PubInv/high-amp-controller-board/PublicInvention_KiCad_Library/Parts/USB User Library-10118194.STEP

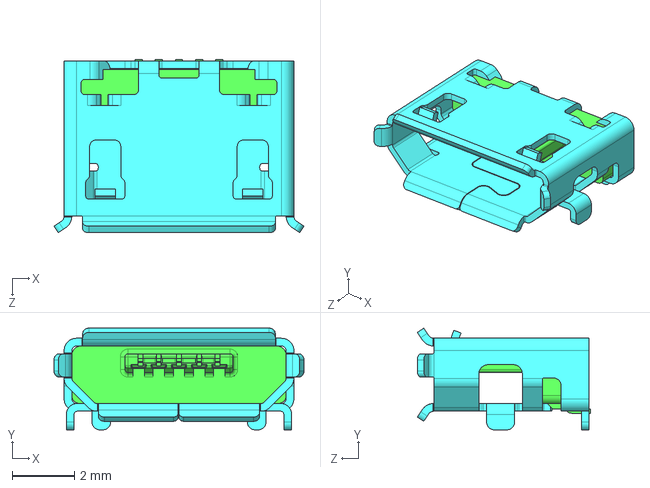
[picture p22: CAD file, 2025-05-26]
PublicInvention_KiCad_Library/Parts/USB User Library-10118194.STEP
8.05 x 3.28 x 5.58 mm
