PubInv/high-amp-controller-board/PublicInvention_KiCad_Library/Parts/12mmx12mm With Green cap.stp

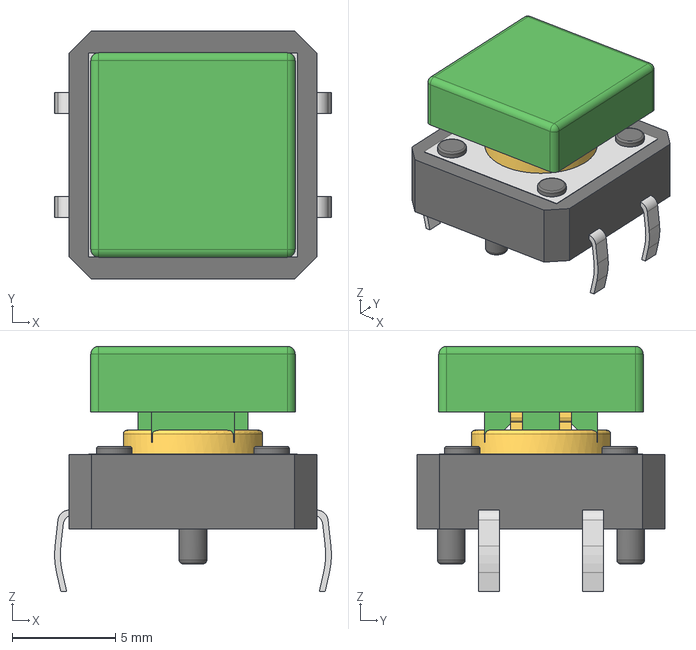
[picture p23: CAD file, 2025-05-26]
PublicInvention_KiCad_Library/Parts/12mmx12mm With Green cap.stp
13.4 x 12.0 x 11.9 mm
Tactal Switch - THRU(12mmx12mmx__mm)-Square Yellow
12mm Cap
