PubInv/high-amp-controller-board/PublicInvention_KiCad_Library/Parts/SOT23.STEP

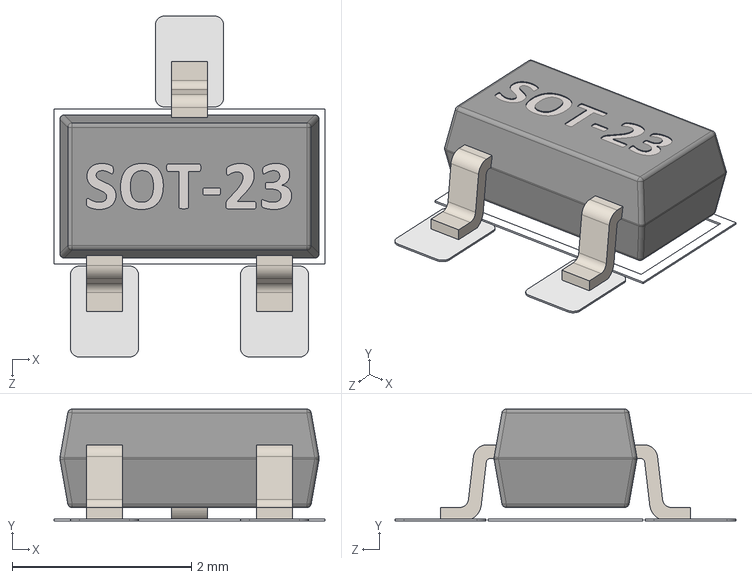
[picture p24: CAD file, 2025-05-26]
PublicInvention_KiCad_Library/Parts/SOT23.STEP
3.03 x 1.25 x 3.81 mm
