PubInv/high-amp-controller-board/PublicInvention_KiCad_Library/Parts/NotGood_XKB Connectivity U254-051N-4BH806.step

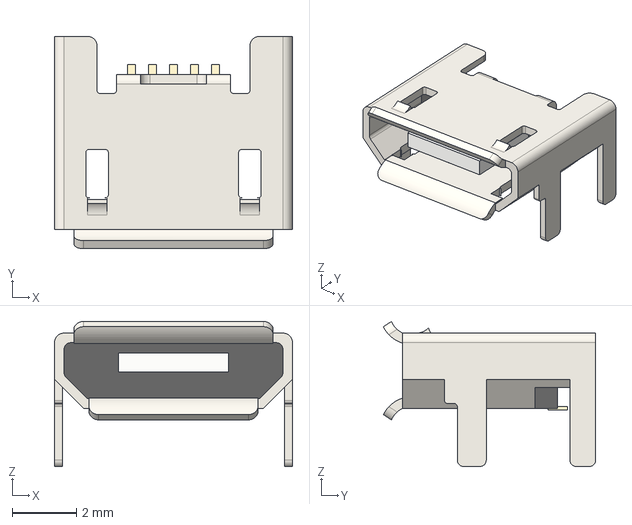
[picture p25: CAD file, 2025-05-26]
PublicInvention_KiCad_Library/Parts/NotGood_XKB Connectivity U254-051N-4BH806.step
7.40 x 6.60 x 4.51 mm
