PubInv/high-amp-controller-board/PublicInvention_KiCad_Library/Parts/BarrelJackSMD v3.step

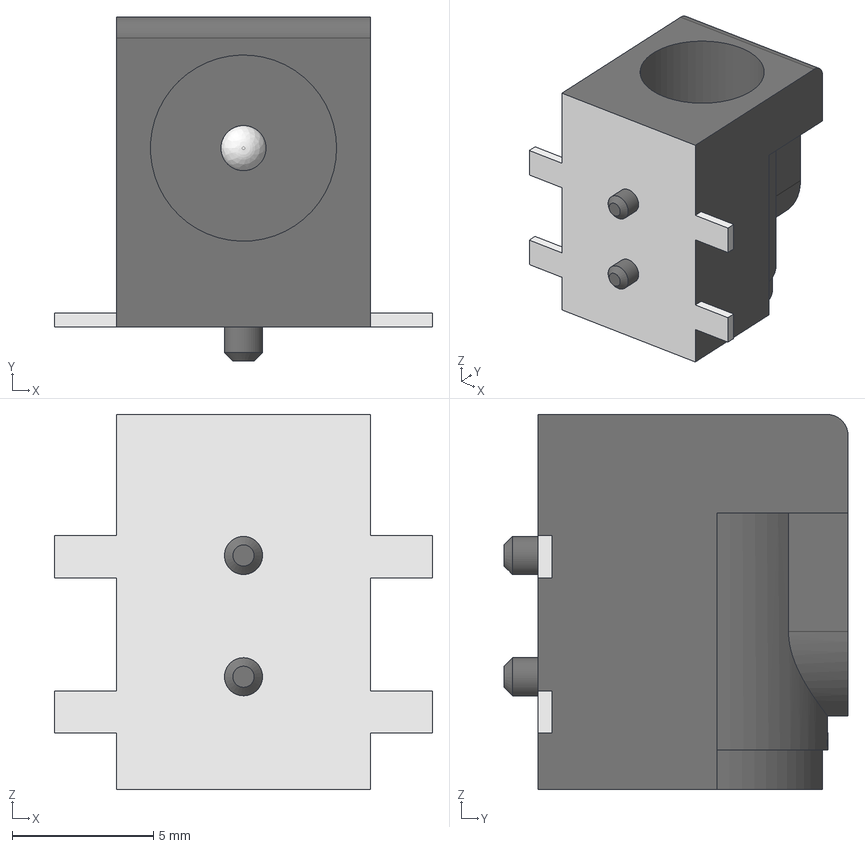
[picture p26: CAD file, 2025-05-26]
PublicInvention_KiCad_Library/Parts/BarrelJackSMD v3.step
13.4 x 12.2 x 13.3 mm
