PubInv/high-amp-controller-board/PublicInvention_KiCad_Library/Parts/TS6-THT-SQ.step

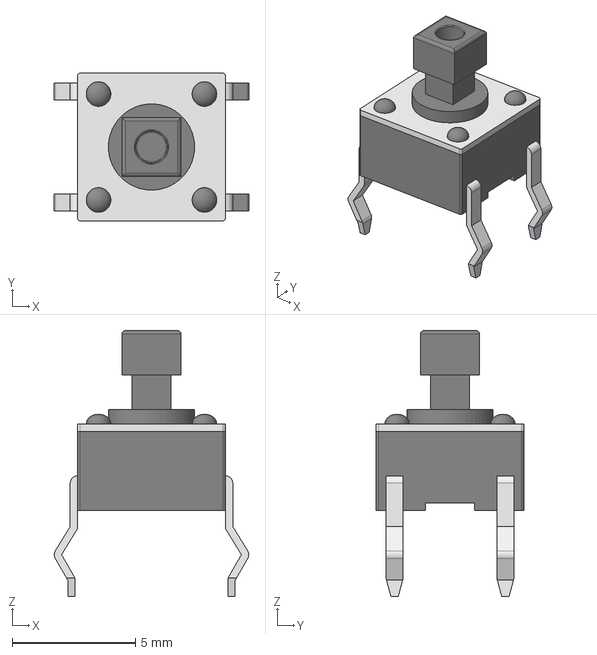
[picture p27: CAD file, 2025-05-26]
PublicInvention_KiCad_Library/Parts/TS6-THT-SQ.step
7.90 x 6.00 x 10.8 mm
