PubInv/high-amp-controller-board/Manufacturing_Files/FabricationPhotos/20250129_134854.jpg

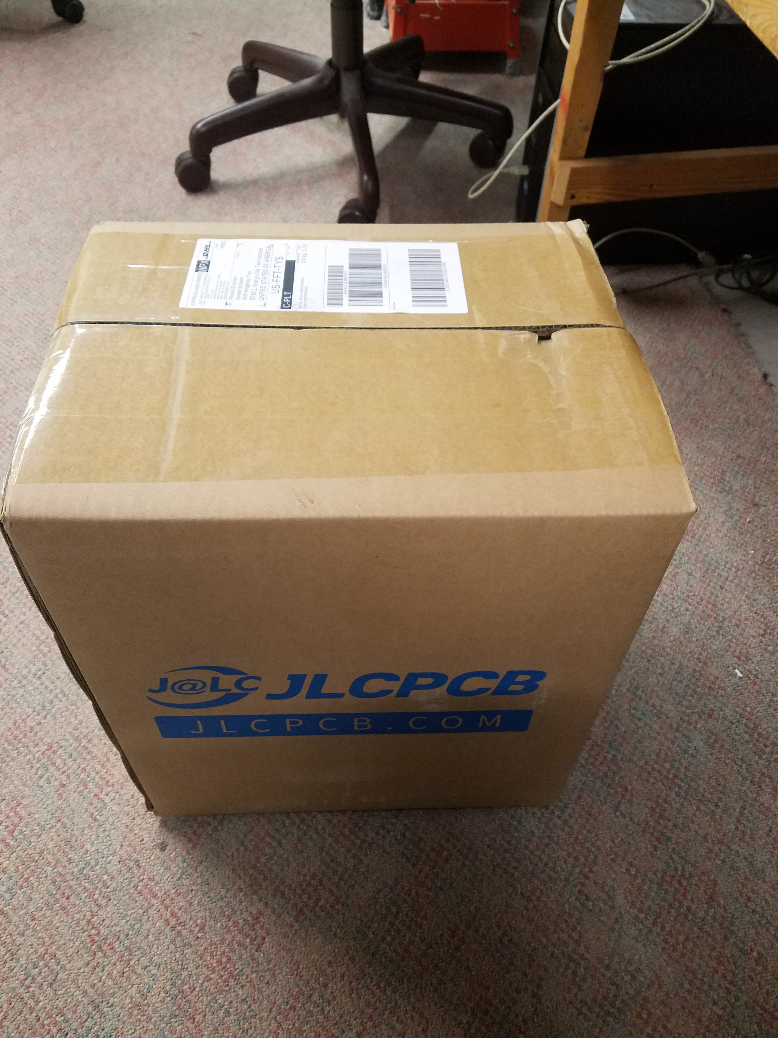
Manufacturing_Files/FabricationPhotos/20250129_134854.jpg
