PubInv/high-amp-controller-board/Adafruit-MAX31850-thermocouple-breakout-board.kicad_sch

## KiCad design Adafruit-MAX31850-thermocouple-breakout-board.kicad_sch (2025-05-26)

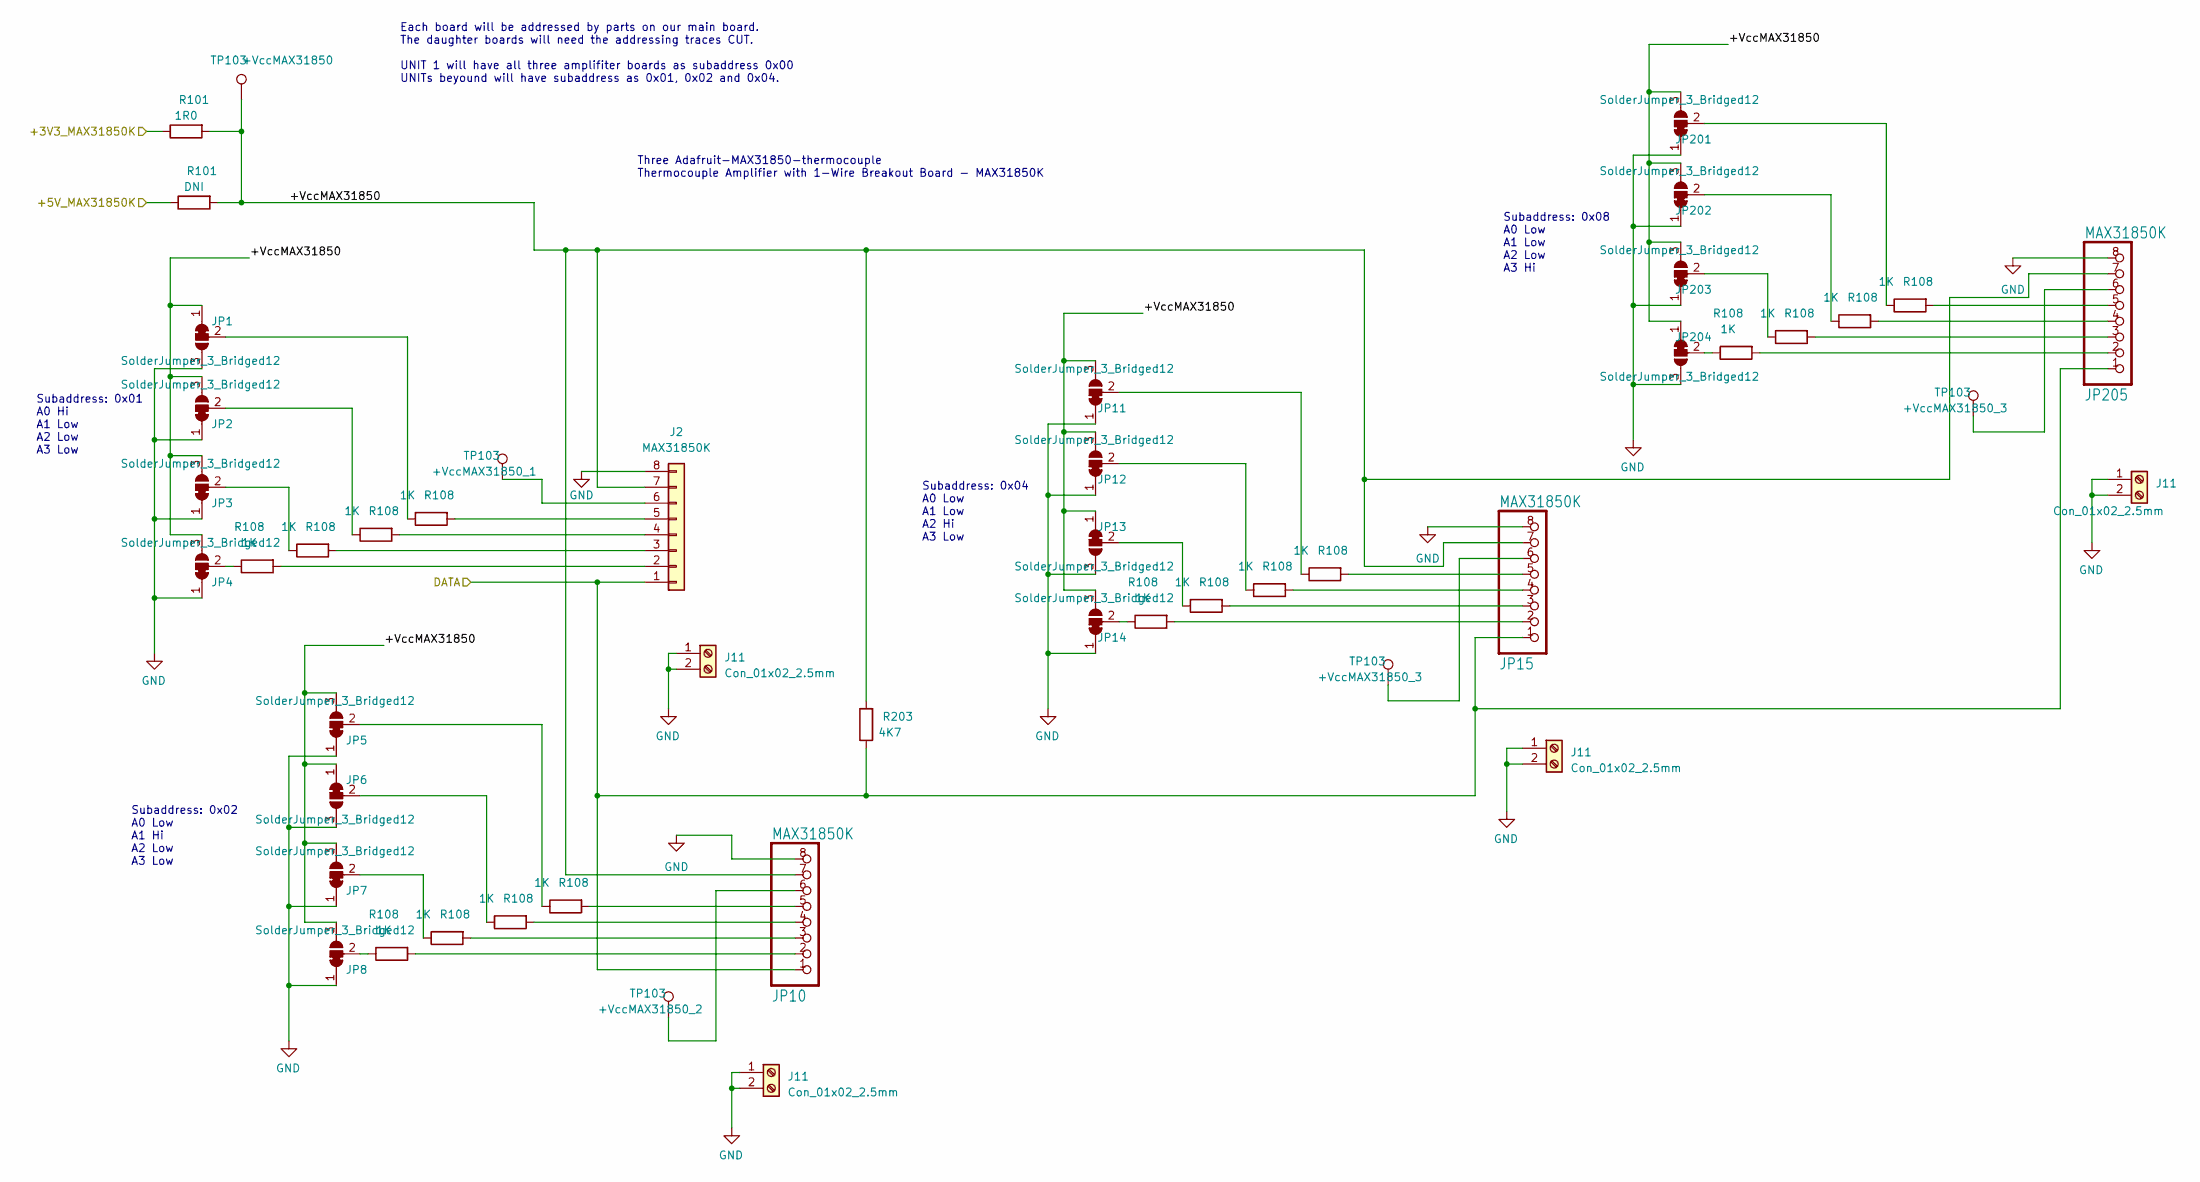
[picture p30: schematic Adafruit-MAX31850-thermocouple-breakout-board.kicad_sch]

Parts:
J2: MAX31850K; Adafruit_MAX31850K_Module; MPN 1727
J11: Con_01x02_2.5mm; JST_XH_B2B-XH-AM_1x02_P2.50mm_Vertical; MPN B2B-XH-A-GU
JP1, JP2, JP3, JP4, JP5, JP6, JP7, JP8, JP11, JP12, JP13, JP14, JP201, JP202, JP203, JP204: SolderJumper_3_Bridged12; SolderJumper-3_P1.3mm_Bridged12_RoundedPad1.0x1.5mm; MPN NA
JP10, JP15, JP205: MAX31850K; Adafruit_MAX31850K_Module; MPN 1727
R101: 1R0; R_0603_1608Metric_Pad0.98x0.95mm_HandSolder; MPN RMC060315%N
R108: 1K; R_0603_1608Metric_Pad0.98x0.95mm_HandSolder; MPN RMC06031K1%N
R203: 4K7; R_0603_1608Metric_Pad0.98x0.95mm_HandSolder; MPN RMC 0603 4K7 F N
TP103: +VccMAX31850; TestPoint_Loop_D2.54mm_Drill1.5mm_Beaded; MPN RH-5000

Connections:
+3V3_MAX31850K: R101.1
+5V_MAX31850K: R101.1
+VccMAX31850: J2.7, JP1.1 (A), JP2.3 (B), JP3.3 (B), JP4.3 (B), JP5.3 (B), JP6.1 (A), JP7.3 (B), JP8.3 (B), JP10.7, JP11.3 (B), JP12.3 (B), JP13.1 (A), JP14.3 (B), JP15.7, JP201.3 (B), JP202.3 (B), JP203.3 (B), JP204.1 (A), JP205.7, R101.2, R203.2, TP103.1
DATA: J2.1, JP10.1, JP15.1, JP205.1, R203.1
GND: J2.8, J11.1, J11.2, JP1.3 (B), JP2.1 (A), JP3.1 (A), JP4.1 (A), JP5.1 (A), JP6.3 (B), JP7.1 (A), JP8.1 (A), JP10.8, JP11.1 (A), JP12.1 (A), JP13.3 (B), JP14.1 (A), JP15.8, JP201.1 (A), JP202.1 (A), JP203.1 (A), JP204.3 (B), JP205.8
unnamed: J2.2, R108.2
unnamed: J2.3, R108.2
unnamed: J2.4, R108.2
unnamed: J2.5, R108.2
unnamed: J2.6, TP103.1
unnamed: JP1.2 (C), R108.1
unnamed: JP2.2 (C), R108.1
unnamed: JP3.2 (C), R108.1
unnamed: JP4.2 (C), R108.1
unnamed: JP5.2 (C), R108.1
unnamed: JP6.2 (C), R108.1
unnamed: JP7.2 (C), R108.1
unnamed: JP8.2 (C), R108.1
unnamed: JP10.2, R108.2
unnamed: JP10.3, R108.2
unnamed: JP10.4, R108.2
unnamed: JP10.5, R108.2
unnamed: JP10.6, TP103.1
unnamed: JP11.2 (C), R108.1
unnamed: JP12.2 (C), R108.1
unnamed: JP13.2 (C), R108.1
unnamed: JP14.2 (C), R108.1
unnamed: JP15.2, R108.2
unnamed: JP15.3, R108.2
unnamed: JP15.4, R108.2
unnamed: JP15.5, R108.2
unnamed: JP15.6, TP103.1
unnamed: JP201.2 (C), R108.1
unnamed: JP202.2 (C), R108.1
unnamed: JP203.2 (C), R108.1
unnamed: JP204.2 (C), R108.1
unnamed: JP205.2, R108.2
unnamed: JP205.3, R108.2
unnamed: JP205.4, R108.2
unnamed: JP205.5, R108.2
unnamed: JP205.6, TP103.1

Notes on the sheet:
Subaddress: 0x02 A0 Low A1 Hi A2 Low A3 Low
Subaddress: 0x04 A0 Low A1 Low A2 Hi A3 Low
Subaddress: 0x01 A0 Hi A1 Low A2 Low A3 Low
Each board will be addressed by parts on our main board. The daughter boards will need the addressing traces CUT. UNIT 1 will have all three amplifiter boards as subaddress 0x00 UNITs beyound will have subaddress as 0x01, 0x02 and 0x04.
Three Adafruit-MAX31850-thermocouple Thermocouple Amplifier with 1-Wire Breakout Board - MAX31850K
Subaddress: 0x08 A0 Low A1 Low A2 Low A3 Hi
