PubInv/high-amp-controller-board/Adafruit-MAX31855-breakout-board.kicad_sch

## KiCad design Adafruit-MAX31855-breakout-board.kicad_sch (2025-05-26)

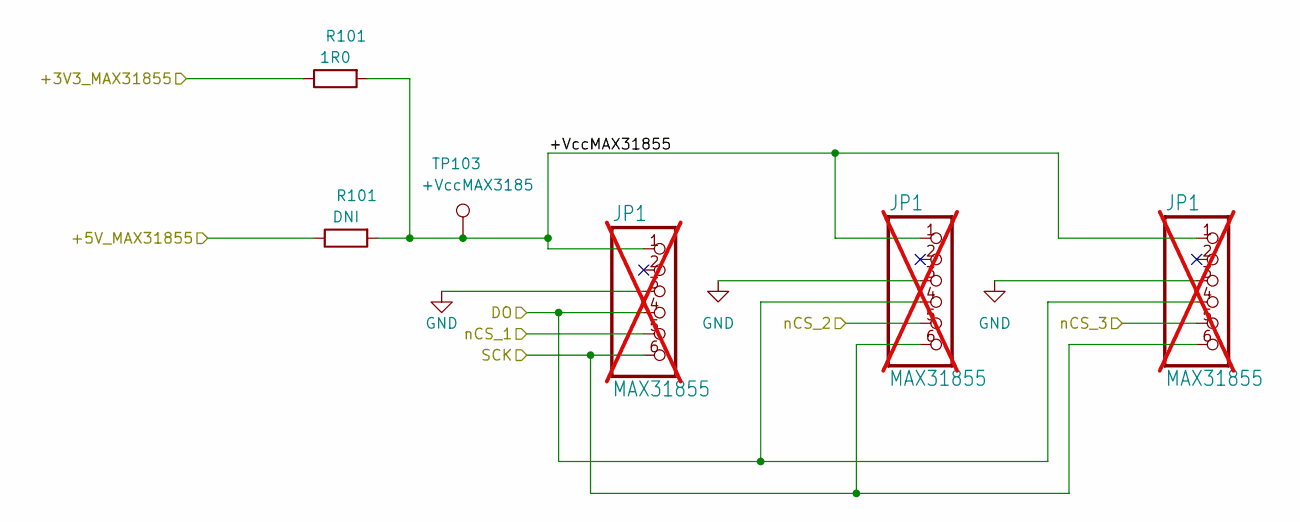
[picture p31: schematic Adafruit-MAX31855-breakout-board.kicad_sch]

Parts:
JP1: MAX31855; Adafruit_MAX31855_Module; MPN 269; not fitted
R101: 1R0; R_0603_1608Metric_Pad0.98x0.95mm_HandSolder; MPN RMC060315%N
TP103: +VccMAX3185; TestPoint_Loop_D2.54mm_Drill1.5mm_Beaded; MPN RH-5000

Connections:
+3V3_MAX31855: R101.1
+5V_MAX31855: R101.1
+VccMAX31855: JP1.1, R101.2, TP103.1
DO: JP1.4
GND: JP1.3
SCK: JP1.6
nCS_1: JP1.5
nCS_2: JP1.5
nCS_3: JP1.5
