PubInv/high-amp-controller-board/Adafruit-MAX31856-PCB-master.kicad_sch

## KiCad design Adafruit-MAX31856-PCB-master.kicad_sch (2025-05-26)

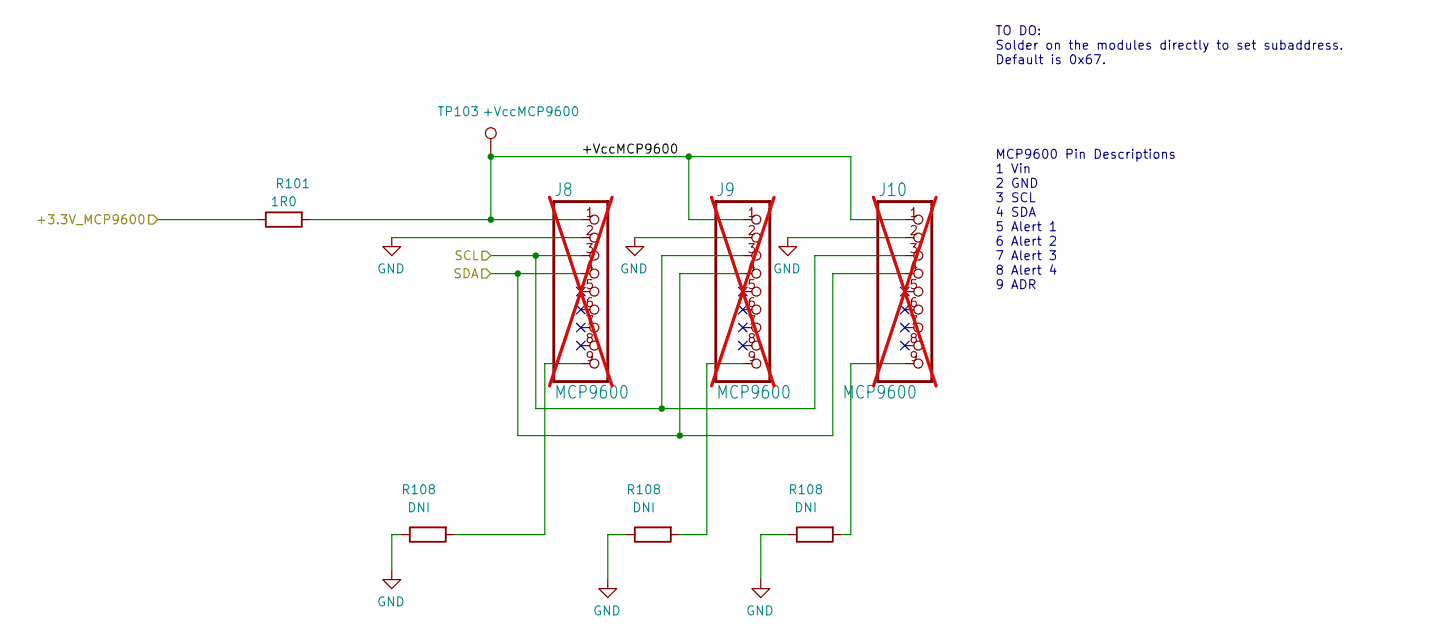
[picture p32: schematic Adafruit-MAX31856-PCB-master.kicad_sch]

Parts:
J8, J9, J10: MCP9600; Adafruit_MCP9600_Module; MPN 4101; not fitted
R101: 1R0; R_0603_1608Metric_Pad0.98x0.95mm_HandSolder; MPN RMC060315%N
R108: DNI; R_0603_1608Metric_Pad0.98x0.95mm_HandSolder; MPN RMC06031K1%N
TP103: +VccMCP9600; TestPoint_Loop_D2.54mm_Drill1.5mm_Beaded; MPN RH-5000

Connections:
+3.3V_MCP9600: R101.1
+VccMCP9600: J8.1, J9.1, J10.1, R101.2, TP103.1
GND: J8.2, J9.2, J10.2, R108.1
unnamed: J8.9, R108.2
unnamed: J9.9, R108.2
unnamed: J10.9, R108.2
SCL: J8.3, J9.3, J10.3
SDA: J8.4, J9.4, J10.4

Notes on the sheet:
MCP9600 Pin Descriptions 1 Vin 2 GND 3 SCL 4 SDA 5 Alert 1 6 Alert 2 7 Alert 3 8 Alert 4 9 ADR
TO DO: Solder on the modules directly to set subaddress. Default is 0x67.
