PubInv/high-amp-controller-board/BreadBoard30P.kicad_sch

## KiCad design BreadBoard30P.kicad_sch (2025-05-26)

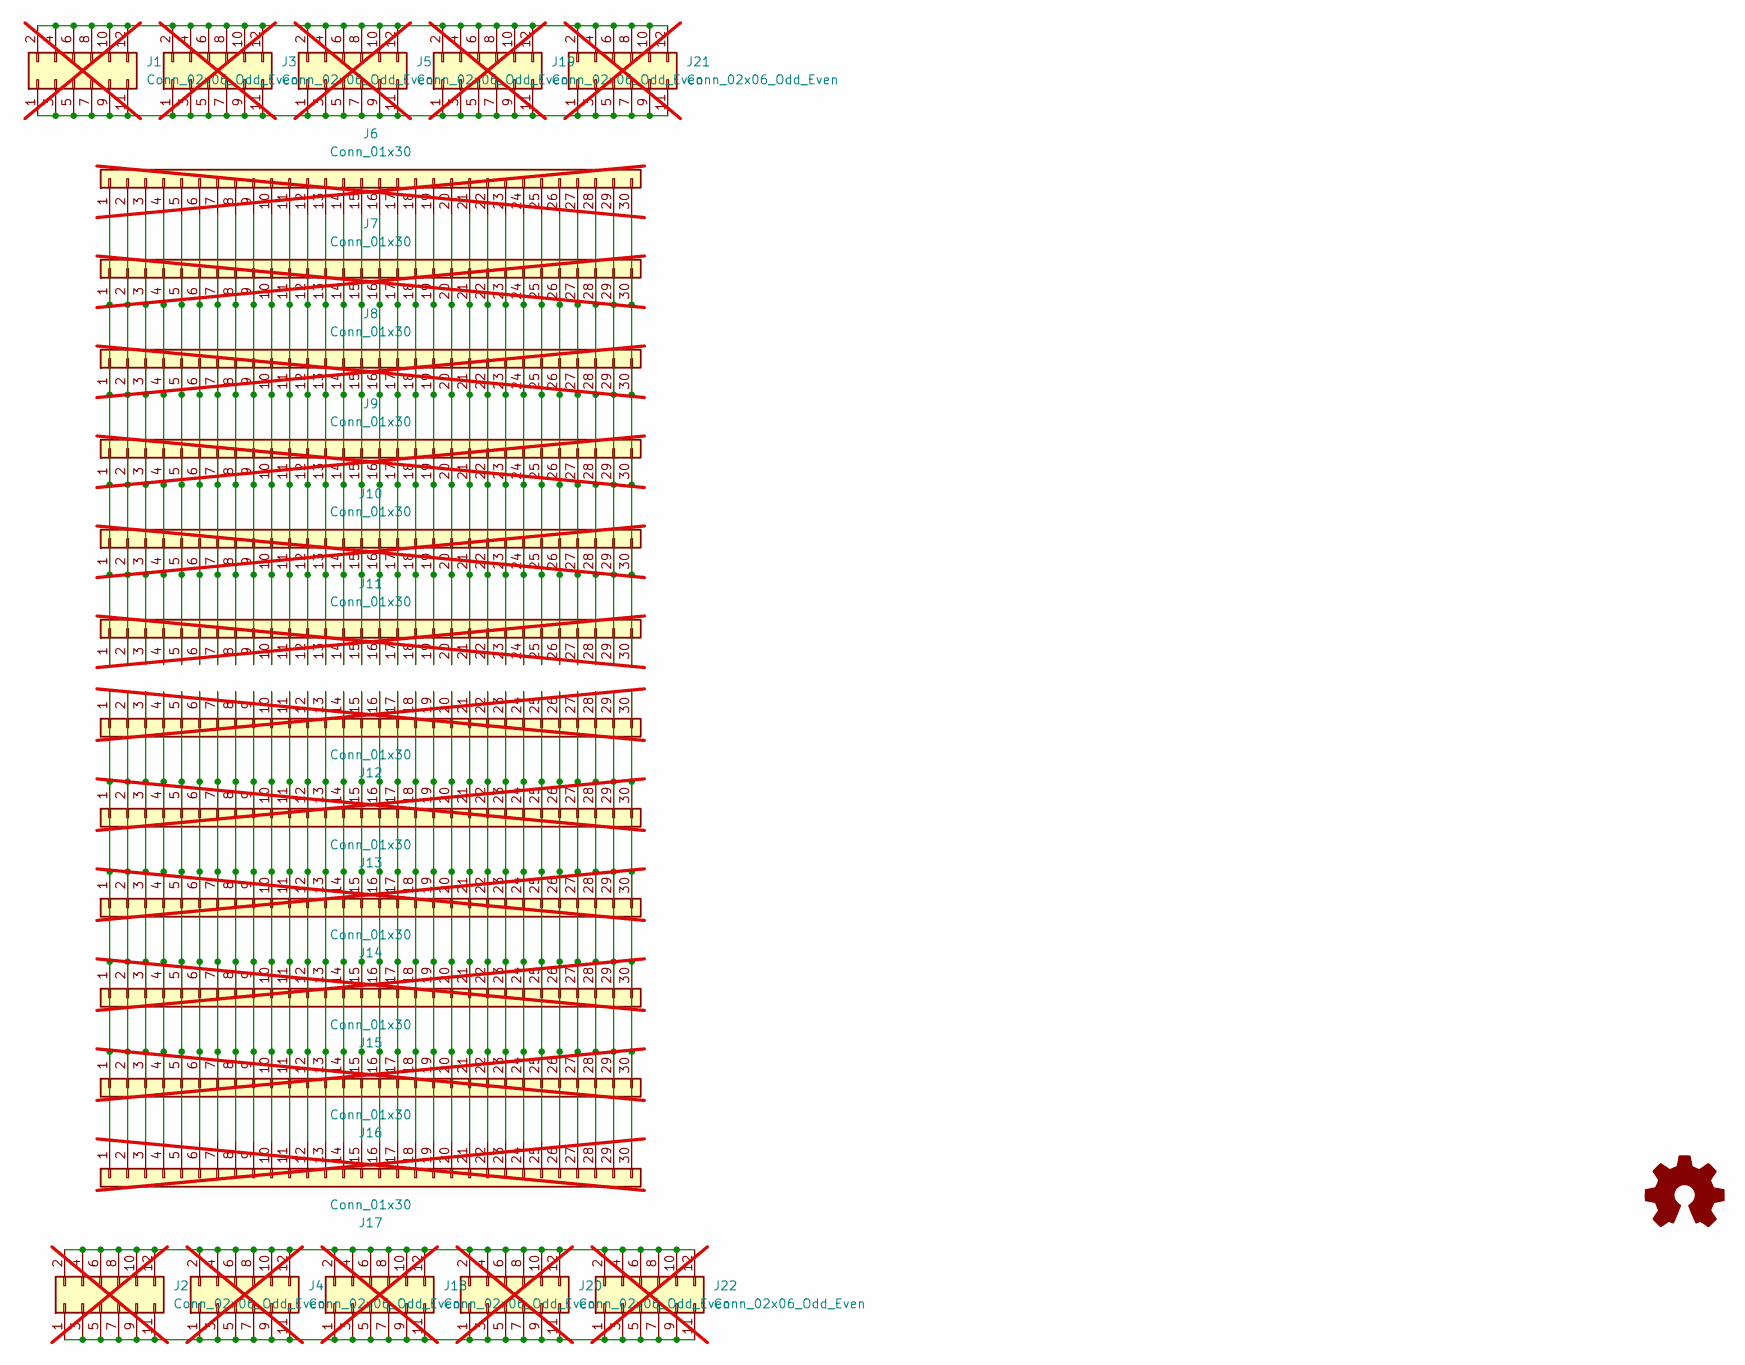
[picture p33: schematic BreadBoard30P.kicad_sch]

Parts:
J1, J2, J3, J4, J5, J18, J19, J20, J21, J22: Conn_02x06_Odd_Even; PinSocket_2x06_P2.54mm_Vertical; not fitted
J6, J7, J8, J9, J10, J11, J12, J13, J14, J15, J16, J17: Conn_01x30; PinSocket_1x30_P2.54mm_Vertical; not fitted

Connections:
unnamed: J1.1, J1.3, J1.5, J1.7, J1.9, J1.11, J3.1, J3.3, J3.5, J3.7, J3.9, J3.11, J5.1, J5.3, J5.5, J5.7, J5.9, J5.11, J19.1, J19.3, J19.5, J19.7, J19.9, J19.11, J21.1, J21.3, J21.5, J21.7, J21.9, J21.11
unnamed: J1.2, J1.4, J1.6, J1.8, J1.10, J1.12, J3.2, J3.4, J3.6, J3.8, J3.10, J3.12, J5.2, J5.4, J5.6, J5.8, J5.10, J5.12, J19.2, J19.4, J19.6, J19.8, J19.10, J19.12, J21.2, J21.4, J21.6, J21.8, J21.10, J21.12
unnamed: J6.1, J7.1, J8.1, J9.1, J10.1, J11.1
unnamed: J6.2, J7.2, J8.2, J9.2, J10.2, J11.2
unnamed: J6.3, J7.3, J8.3, J9.3, J10.3, J11.3
unnamed: J6.4, J7.4, J8.4, J9.4, J10.4, J11.4
unnamed: J6.5, J7.5, J8.5, J9.5, J10.5, J11.5
unnamed: J6.6, J7.6, J8.6, J9.6, J10.6, J11.6
unnamed: J6.7, J7.7, J8.7, J9.7, J10.7, J11.7
unnamed: J6.8, J7.8, J8.8, J9.8, J10.8, J11.8
unnamed: J6.9, J7.9, J8.9, J9.9, J10.9, J11.9
unnamed: J6.10, J7.10, J8.10, J9.10, J10.10, J11.10
unnamed: J6.11, J7.11, J8.11, J9.11, J10.11, J11.11
unnamed: J6.12, J7.12, J8.12, J9.12, J10.12, J11.12
unnamed: J6.13, J7.13, J8.13, J9.13, J10.13, J11.13
unnamed: J6.14, J7.14, J8.14, J9.14, J10.14, J11.14
unnamed: J6.15, J7.15, J8.15, J9.15, J10.15, J11.15
unnamed: J6.16, J7.16, J8.16, J9.16, J10.16, J11.16
unnamed: J6.17, J7.17, J8.17, J9.17, J10.17, J11.17
unnamed: J6.18, J7.18, J8.18, J9.18, J10.18, J11.18
unnamed: J6.19, J7.19, J8.19, J9.19, J10.19, J11.19
unnamed: J6.20, J7.20, J8.20, J9.20, J10.20, J11.20
unnamed: J6.21, J7.21, J8.21, J9.21, J10.21, J11.21
unnamed: J6.22, J7.22, J8.22, J9.22, J10.22, J11.22
unnamed: J6.23, J7.23, J8.23, J9.23, J10.23, J11.23
unnamed: J6.24, J7.24, J8.24, J9.24, J10.24, J11.24
unnamed: J6.25, J7.25, J8.25, J9.25, J10.25, J11.25
unnamed: J6.26, J7.26, J8.26, J9.26, J10.26, J11.26
unnamed: J6.27, J7.27, J8.27, J9.27, J10.27, J11.27
unnamed: J6.28, J7.28, J8.28, J9.28, J10.28, J11.28
unnamed: J6.29, J7.29, J8.29, J9.29, J10.29, J11.29
unnamed: J6.30, J7.30, J8.30, J9.30, J10.30, J11.30
unnamed: J12.1, J13.1, J14.1, J15.1, J16.1, J17.1
unnamed: J12.2, J13.2, J14.2, J15.2, J16.2, J17.2
unnamed: J12.3, J13.3, J14.3, J15.3, J16.3, J17.3
unnamed: J12.4, J13.4, J14.4, J15.4, J16.4, J17.4
unnamed: J12.5, J13.5, J14.5, J15.5, J16.5, J17.5
unnamed: J12.6, J13.6, J14.6, J15.6, J16.6, J17.6
unnamed: J12.7, J13.7, J14.7, J15.7, J16.7, J17.7
unnamed: J12.8, J13.8, J14.8, J15.8, J16.8, J17.8
unnamed: J12.9, J13.9, J14.9, J15.9, J16.9, J17.9
unnamed: J12.10, J13.10, J14.10, J15.10, J16.10, J17.10
unnamed: J12.11, J13.11, J14.11, J15.11, J16.11, J17.11
unnamed: J12.12, J13.12, J14.12, J15.12, J16.12, J17.12
unnamed: J12.13, J13.13, J14.13, J15.13, J16.13, J17.13
unnamed: J12.14, J13.14, J14.14, J15.14, J16.14, J17.14
unnamed: J12.15, J13.15, J14.15, J15.15, J16.15, J17.15
unnamed: J12.16, J13.16, J14.16, J15.16, J16.16, J17.16
unnamed: J12.17, J13.17, J14.17, J15.17, J16.17, J17.17
unnamed: J12.18, J13.18, J14.18, J15.18, J16.18, J17.18
unnamed: J12.19, J13.19, J14.19, J15.19, J16.19, J17.19
unnamed: J12.20, J13.20, J14.20, J15.20, J16.20, J17.20
unnamed: J12.21, J13.21, J14.21, J15.21, J16.21, J17.21
unnamed: J12.22, J13.22, J14.22, J15.22, J16.22, J17.22
unnamed: J12.23, J13.23, J14.23, J15.23, J16.23, J17.23
unnamed: J12.24, J13.24, J14.24, J15.24, J16.24, J17.24
unnamed: J12.25, J13.25, J14.25, J15.25, J16.25, J17.25
unnamed: J12.26, J13.26, J14.26, J15.26, J16.26, J17.26
unnamed: J12.27, J13.27, J14.27, J15.27, J16.27, J17.27
unnamed: J12.28, J13.28, J14.28, J15.28, J16.28, J17.28
unnamed: J12.29, J13.29, J14.29, J15.29, J16.29, J17.29
unnamed: J12.30, J13.30, J14.30, J15.30, J16.30, J17.30
unnamed: J2.1, J2.3, J2.5, J2.7, J2.9, J2.11, J4.1, J4.3, J4.5, J4.7, J4.9, J4.11, J18.1, J18.3, J18.5, J18.7, J18.9, J18.11, J20.1, J20.3, J20.5, J20.7, J20.9, J20.11, J22.1, J22.3, J22.5, J22.7, J22.9, J22.11
unnamed: J2.2, J2.4, J2.6, J2.8, J2.10, J2.12, J4.2, J4.4, J4.6, J4.8, J4.10, J4.12, J18.2, J18.4, J18.6, J18.8, J18.10, J18.12, J20.2, J20.4, J20.6, J20.8, J20.10, J20.12, J22.2, J22.4, J22.6, J22.8, J22.10, J22.12
