PubInv/high-amp-controller-board/Control_1v2.kicad_sch

## KiCad design Control_1v2.kicad_sch (2025-05-26)

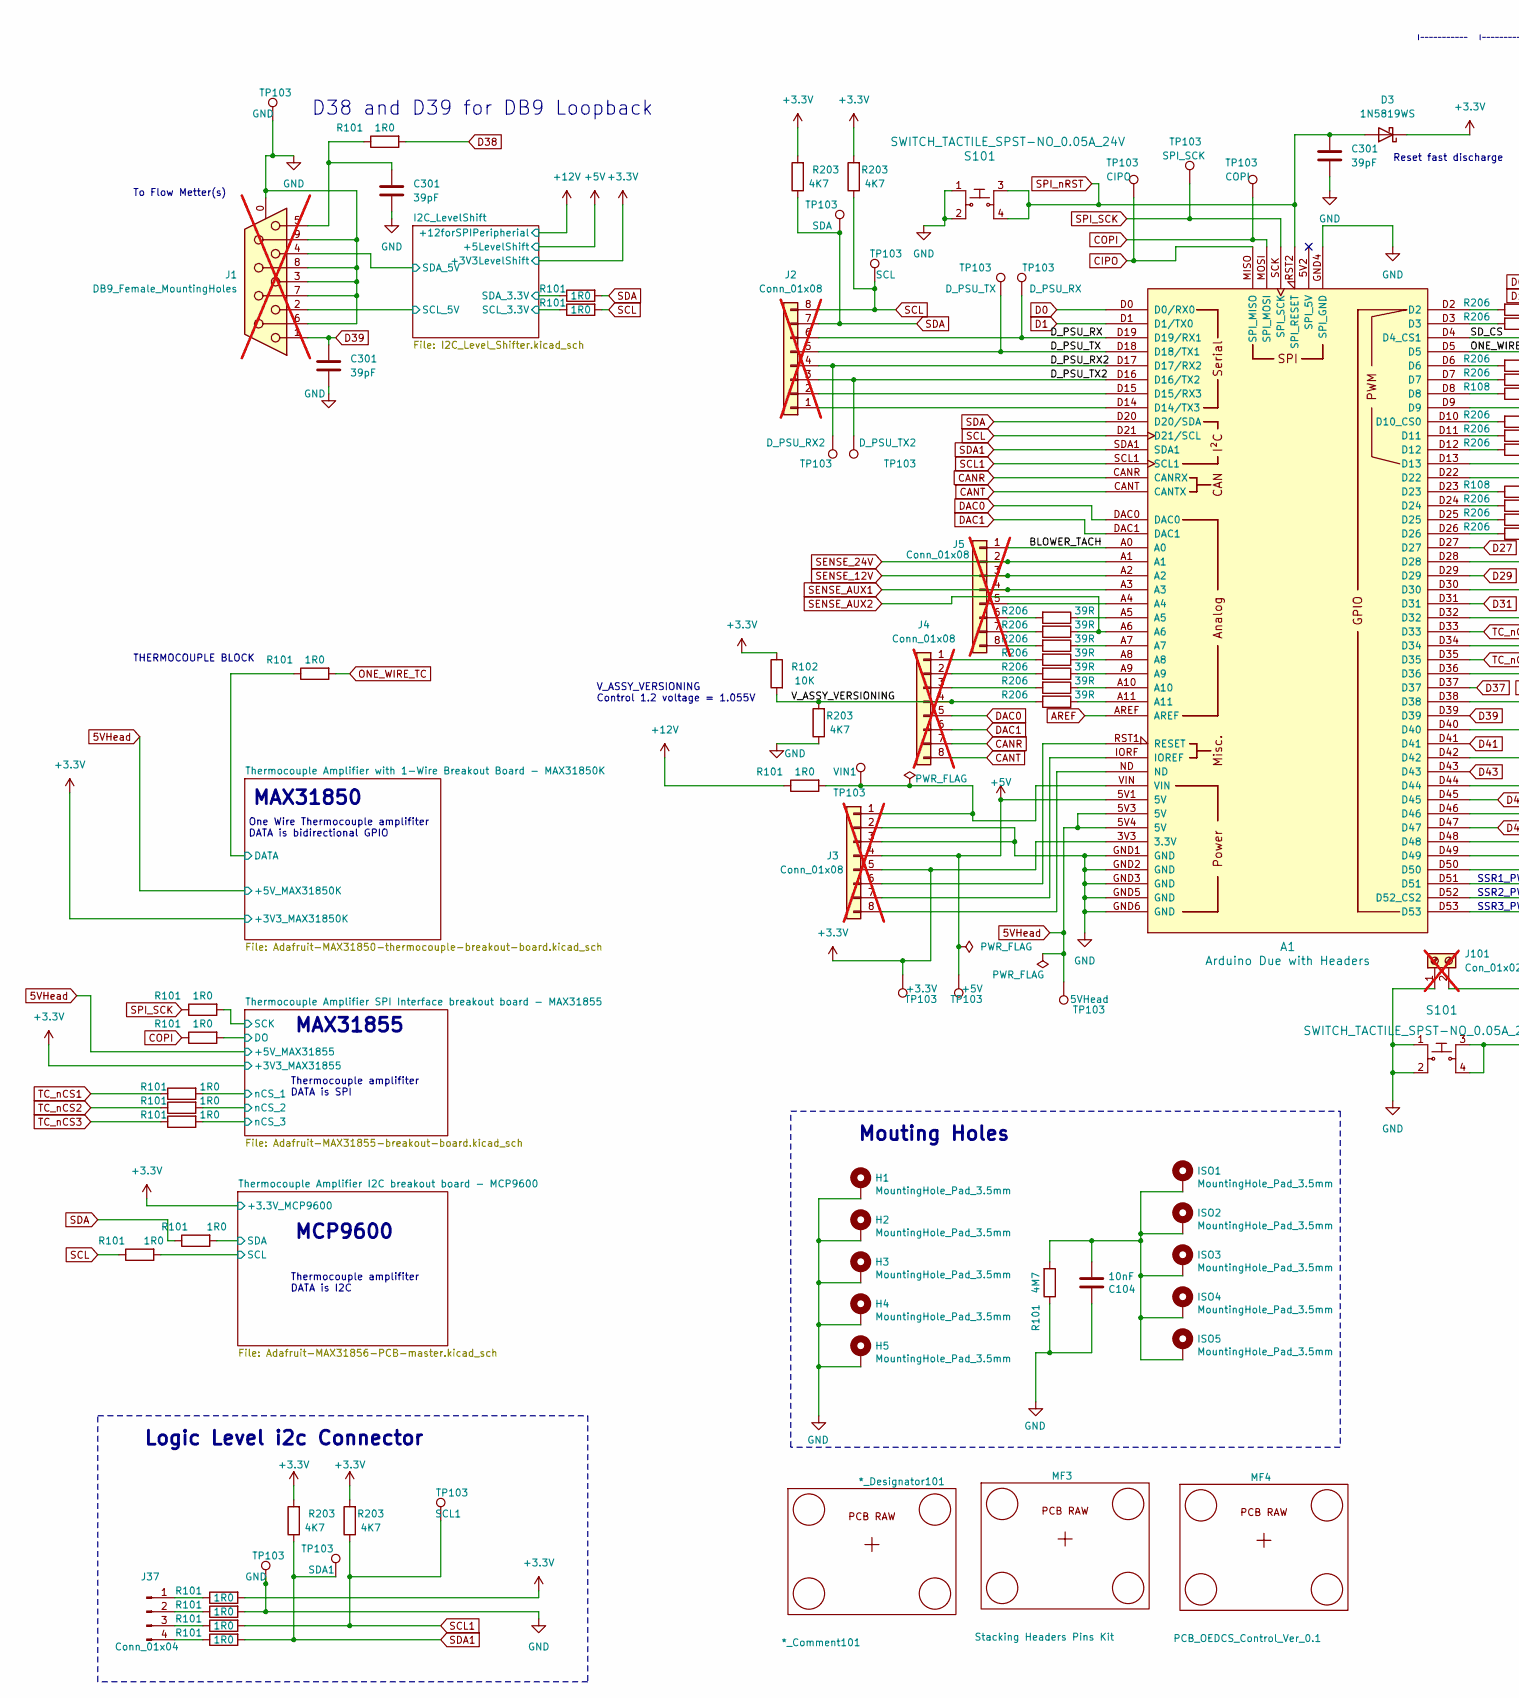
[picture p34: schematic Control_1v2.kicad_sch, part in row 1, column 1]

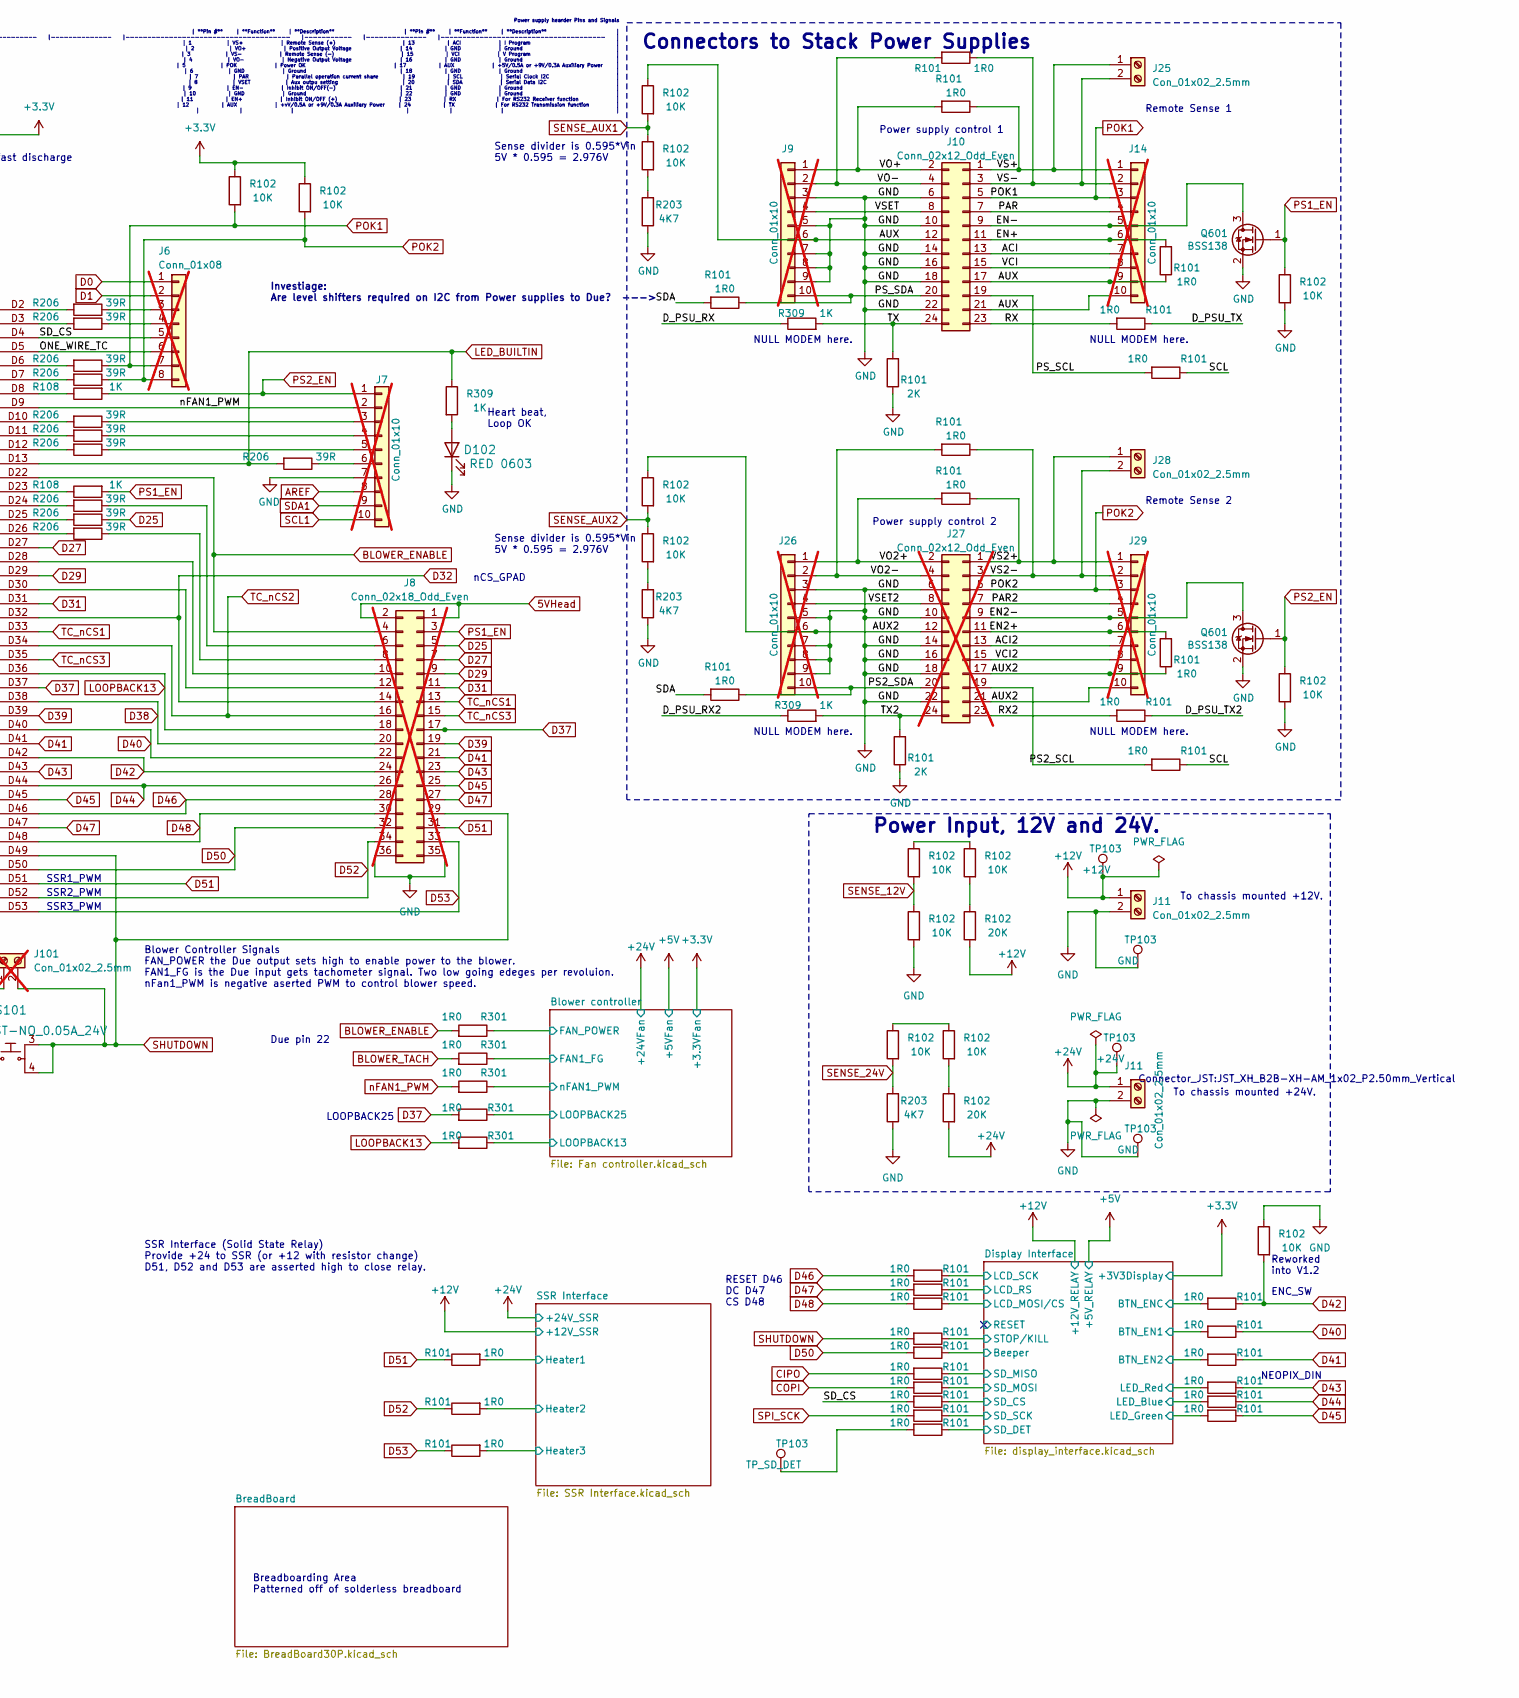
[picture p35: schematic Control_1v2.kicad_sch, part in row 1, column 2]

Parts:
*_Designator101: *_Comment101; Footprint; MPN na
A1: Arduino Due with Headers; Arduino_Due_Shield_Annotated; MPN DUE
C104: 10nF; C_0603_1608Metric_Pad1.08x0.95mm_HandSolder; MPN CC0603JRNPO9BN103
C301: 39pF; C_0603_1608Metric_Pad1.08x0.95mm_HandSolder; MPN CC0603JRNPO9BN390
D3: 1N5819WS; D_SOD-323; MPN 1N5819WS
D102: RED 0603; LED_0603_1608Metric_Pad1.05x0.95mm_HandSolder; MPN LTST-C171KRKT; Digi-Key_PN 160-1427-1-ND
H1, H2, H3, H4, H5: MountingHole_Pad_3.5mm; MountingHole_3.5mm_Pad_Via
ISO1, ISO2, ISO3, ISO4, ISO5: MountingHole_Pad_3.5mm; MountingHole_3.5mm_Pad_Via
J1: DB9_Female_MountingHoles; DSUB-9_Female_Horizontal_P2.77x2.84mm_EdgePinOffset4.94mm_H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; MPN D-DMR009PF-D002; not fitted
J2, J3, J4, J5, J6: Conn_01x08; PinSocket_1x08_P2.54mm_Vertical; MPN PZ254-1-08-Z-8.5; not fitted
J7, J9, J14, J26, J29: Conn_01x10; PinSocket_1x10_P2.54mm_Vertical; MPN PZ254-1-10-Z-8.5; not fitted
J8: Conn_02x18_Odd_Even; PinSocket_2x18_P2.54mm_Vertical; not fitted
J10: Conn_02x12_Odd_Even; JST_PHD_B24B-PHDSS_2x12_P2.00mm_Vertical; Part Number B24B-PHDSS
J11, J25, J28: Con_01x02_2.5mm; JST_XH_B2B-XH-AM_1x02_P2.50mm_Vertical; MPN B2B-XH-A-GU
J27: Conn_02x12_Odd_Even; JST_PHD_B24B-PHDSS_2x12_P2.00mm_Vertical; Part Number B24B-PHDSS; not fitted
J37: Conn_01x04; PinHeader_1x04_P2.54mm_Vertical; MPN HB-PH3-25414PB2GOP
J101: Con_01x02_2.5mm; JST_XH_B2B-XH-AM_1x02_P2.50mm_Vertical; MPN B2B-XH-A-GU; not fitted
MF3: Stacking Headers Pins Kit; NA; MPN PCB_BKT_OEDCS_01
MF4: PCB_OEDCS_Control_Ver_0.1; NA; MPN PCB_OEDCS_Control_Ver_0.1
Q601: BSS138; SOT-23; MPN BSS138
R101, R301: 1R0; R_0603_1608Metric_Pad0.98x0.95mm_HandSolder; MPN RMC060315%N
R102: 10K; R_0603_1608Metric_Pad0.98x0.95mm_HandSolder; MPN RMC060310KFN
R108, R309: 1K; R_0603_1608Metric_Pad0.98x0.95mm_HandSolder; MPN RMC06031K1%N
R203: 4K7; R_0603_1608Metric_Pad0.98x0.95mm_HandSolder; MPN RMC 0603 4K7 F N
R206: 39R; R_0603_1608Metric_Pad0.98x0.95mm_HandSolder; MPN RMC0603391%N
S101: SWITCH_TACTILE_SPST-NO_0.05A_24V; Switch_Tactile_THT_6x6mm; MPN TE Connectivity 1825910-7, Dongguan Gua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
TP103: SPI_SCK; TestPoint_Loop_D2.54mm_Drill1.5mm_Beaded; MPN RH-5004

Connections:
5VHead: A1.5V3 (5V), A1.5V4 (5V), J8.1, J8.2, TP103.1
+3.3V: A1.3V3 (3.3V), D3.1 (K), J3.5, R101.2, R102.1, R203.2, TP103.1
+5V: A1.5V1 (5V), J3.4, TP103.1
+12V: J11.1, R101.1, R102.2, TP103.1
+24V: J11.1, R102.2, TP103.1
ACI: J10.13, J14.7
ACI2: J27.13, J29.7
AREF: A1.AREF, J7.8
AUX: J9.6, J10.12, J10.17, J10.21, J14.9, J14.10, R101.1, R102.1
AUX2: J26.6, J27.12, J27.17, J27.21, J29.9, J29.10, R101.1, R102.1
BLOWER_ENABLE: A1.D22, J8.4, R301.2
BLOWER_TACH: A1.A0, J5.1, R301.2
BTN_EN1: R101.2
BTN_EN2: R101.2
BTN_ENC: R101.2
Beeper: R101.1
CANR: A1.CANR (CANRX), J4.7
CANT: A1.CANT (CANTX), J4.8
CIPO: A1.MISO (SPI_MISO), R101.2, TP103.1
COPI: A1.MOSI (SPI_MOSI), R101.1, R101.2, TP103.1
D0: A1.D0 (D0/RX0), J6.1
D1: A1.D1 (D1/TX0), J6.2
D25: J8.5, R206.1
D27: A1.D27, J8.7
D29: A1.D29, J8.9
D31: A1.D31, J8.11
D32: A1.D32, J8.14
D37: A1.D37, J8.17, R301.2
D38: A1.D38, J8.20, R101.2
D39: A1.D39, C301.1, J1.1, J8.19
D40: A1.D40, J8.22, R101.1
D41: A1.D41, J8.21, R101.1
D42: A1.D42, J8.24, R101.1, R102.2
D43: A1.D43, J8.23, R101.1
D44: A1.D44, J8.26, R101.1
D45: A1.D45, J8.25, R101.1
D46: A1.D46, J8.28, R101.2
D47: A1.D47, J8.27, R101.2
D48: A1.D48, J8.30, R101.2
D50: A1.D50, J8.32, R101.2
D51: A1.D51, J8.31, R101.1
D52: A1.D52 (D52_CS2), J8.34, R101.1
D53: A1.D53, J8.33, R101.1
DAC0: A1.DAC0, J4.5
DAC1: A1.DAC1, J4.6
DATA: R101.1
DO: R101.2
D_PSU_RX: A1.D19 (D19/RX1), J2.6, R309.1, TP103.1
D_PSU_RX2: A1.D17 (D17/RX2), J2.4, R309.1, TP103.1
D_PSU_TX: A1.D18 (D18/TX1), J2.5, R101.1, TP103.1
D_PSU_TX2: A1.D16 (D16/TX2), J2.3, R101.1, TP103.1
EN2+: J27.11, J29.6, R101.2
EN2-: J27.9, J29.5, Q601.3 (D)
EN+: J10.11, J14.6, R101.2
EN-: J10.9, J14.5, Q601.3 (D)
FAN1_FG: R301.1
FAN_POWER: R301.1
GND: A1.GND1 (GND), A1.GND2 (GND), A1.GND3 (GND), A1.GND4 (SPI_GND), A1.GND5 (GND), A1.GND6 (GND), C104.1, C301.2, D102.1 (K), H1.1, H2.1, H3.1, H4.1, H5.1, J1.0 (PAD), J1.3, J1.6, J1.7, J1.8, J1.9, J3.2, J3.3, J7.7, J8.35, J8.36, J9.3, J9.5, J9.7, J9.8, J9.9, J10.6, J10.10, J10.14, J10.16, J10.18, J10.22, J11.2, J26.3, J26.5, J26.7, J26.8, J26.9, J27.6, J27.10, J27.14, J27.16, J27.18, J27.22, J101.1, Q601.2 (S), R101.1, R101.2, R102.1, R102.2, R203.1, S101.1, S101.2, TP103.1
Heater1: R101.2
Heater2: R101.2
Heater3: R101.2
LCD_MOSI/CS: R101.1
LCD_RS: R101.1
LCD_SCK: R101.1
LED_BUILTIN: A1.D13, R206.2, R309.1
LED_Blue: R101.2
LED_Green: R101.2
LED_Red: R101.2
LOOPBACK13: A1.D36, J8.18, R301.1, R301.2
LOOPBACK25: R301.1
unnamed: A1.A4, J5.5
unnamed: A1.A5, R206.1
unnamed: A1.A7, R206.1
unnamed: A1.A8, R206.1
unnamed: A1.A9, R206.1
unnamed: A1.A10, R206.1
unnamed: A1.A11, R206.1
unnamed: A1.D2, R206.2
unnamed: A1.D3, R206.2
unnamed: A1.D6, R206.2
unnamed: A1.D7, R206.2
unnamed: A1.D8, R108.1
unnamed: A1.D10 (D10_CS0), R206.2
unnamed: A1.D11, R206.2
unnamed: A1.D12, R206.2
unnamed: A1.D14 (D14/TX3), J2.1
unnamed: A1.D15 (D15/RX3), J2.2
unnamed: A1.D23, R108.1
unnamed: A1.D24, R206.2
unnamed: A1.D25, R206.2
unnamed: A1.D26, R206.2
unnamed: A1.D28, J8.10
unnamed: A1.D30, J8.12
unnamed: A1.IORF (IOREF), J3.7
unnamed: A1.ND, J3.8
unnamed: A1.RST1 (RESET), J3.6
unnamed: A1.VIN, J3.1, R101.2, TP103.1
unnamed: C104.2, ISO1.1, ISO2.1, ISO3.1, ISO4.1, ISO5.1, R101.2
unnamed: C301.1, J1.5, R101.1
unnamed: D102.2 (A), R309.2
unnamed: J4.1, R206.2
unnamed: J4.2, R206.2
unnamed: J4.3, R206.2
unnamed: J5.6, R206.2
unnamed: J5.7, R206.2
unnamed: J5.8, R206.2
unnamed: J6.3, R206.1
unnamed: J6.4, R206.1
unnamed: J7.3, R206.1
unnamed: J7.4, R206.1
unnamed: J7.5, R206.1
unnamed: J7.6, R206.1
unnamed: J8.6, R206.1
unnamed: J8.8, R206.1
unnamed: J37.1, R101.1
unnamed: J37.2, R101.1
unnamed: J37.3, R101.1
unnamed: J37.4, R101.1
unnamed: R101.2, TP103.1
unnamed: R102.1, R102.2
unnamed: R102.2, R203.2
ONE_WIRE_TC: A1.D5, J6.6, R101.2
PAR: J10.7, J14.4
PAR2: J27.7, J29.4
POK1: J6.7, J10.5, J14.3, R102.2, R206.1
POK2: J6.8, J27.5, J29.3, R102.2, R206.1
PS1_EN: J8.3, Q601.1 (G), R102.1, R108.2
PS2_EN: J7.1, Q601.1 (G), R102.1, R108.2
PS2_SCL: J27.19, R101.2
PS2_SDA: J26.10, J27.20, R101.1
PS_SCL: J10.19, R101.2
PS_SDA: J9.10, J10.20, R101.1
RX: J10.23, R101.2
RX2: J27.23, R101.2
SCK: R101.2
SCL: A1.D21 (D21/SCL), J2.8, R101.1, R101.2, R203.1, TP103.1
SCL1: A1.SCL1, J7.10, R101.2, R203.1, TP103.1
SCL_3.3V: R101.1
SCL_5V: J1.2
SDA: A1.D20 (D20/SDA), J2.7, R101.1, R101.2, R203.1, TP103.1
SDA1: A1.SDA1, J7.9, R101.2, R203.1, TP103.1
SDA_3.3V: R101.1
SDA_5V: J1.4
SD_CS: A1.D4 (D4_CS1), J6.5, R101.1, R101.2
SD_DET: R101.1
SD_MISO: R101.1
SD_MOSI: R101.1
SD_SCK: R101.1
SENSE_12V: A1.A2, J5.3, R102.1, R102.2
SENSE_24V: A1.A1, J5.2, R102.2, R203.2
SENSE_AUX1: A1.A3, J5.4, R102.1, R102.2
SENSE_AUX2: A1.A6, R102.1, R102.2, R206.1
SHUTDOWN: A1.D49, J8.29, J101.2, R101.2, S101.3, S101.4
SPI_SCK: A1.SCK (SPI_SCK), R101.1, R101.2, TP103.1
SPI_nRST: A1.RST2 (SPI_RESET), C301.1, D3.2 (A), S101.3, S101.4
STOP/KILL: R101.1
TC_nCS1: A1.D33, J8.13, R101.1
TC_nCS2: A1.D34, J8.16, R101.1
TC_nCS3: A1.D35, J8.15, R101.1
TX: J10.24, R101.2, R309.2
TX2: J27.24, R101.2, R309.2
VCI: J10.15, J14.8
VCI2: J27.15, J29.8
VO2+: J26.1, J27.2, R101.2
VO2-: J26.2, J27.4, R101.2
VO+: J9.1, J10.2, R101.2
VO-: J9.2, J10.4, R101.2
VS2+: J27.1, J28.1, J29.1, R101.1
VS2-: J27.3, J28.2, J29.2, R101.1
VS+: J10.1, J14.1, J25.1, R101.1
VS-: J10.3, J14.2, J25.2, R101.1
VSET: J9.4, J10.8
VSET2: J26.4, J27.8
V_ASSY_VERSIONING: J4.4, R102.2, R203.2, R206.2
nCS_1: R101.2
nCS_2: R101.2
nCS_3: R101.2
nFAN1_PWM: A1.D9, J7.2, R301.1, R301.2

Notes on the sheet:
Reset fast discharge
MCP9600
To Flow Metter(s)
SSR Interface (Solid State Relay) Provide +24 to SSR (or +12 with resistor change) D51, D52 and D53 are asserted high to close relay.
SSR2_PWM
LOOPBACK25
To chassis mounted +12V.
SSR3_PWM
NULL MODEM here.
Remote Sense 1
Power Input, 12V and 24V.
ENC_SW
Blower Controller Signals FAN_POWER the Due output sets high to enable power to the blower. FAN1_FG is the Due input gets tachometer signal. Two low going edeges per revoluion. nFan1_PWM is negative aserted PWM to control blower speed.
NEOPIX_DIN
Investiage: Are level shifters required on I2C from Power supplies to Due? --->
Logic Level i2c Connector
Power supply control 2
Thermocouple amplifiter DATA is I2C
THERMOCOUPLE BLOCK
Mouting Holes
Power supply control 1
Connectors to Stack Power Supplies
Thermocouple amplifiter DATA is SPI
nCS_GPAD
Power supply hearder Pins and Signals | **Pin #** | **Function** | **Description** | **Pin #** | **Function** | **Description** | |----------- |-------------- |-------------------------------------- |----------- |-------------- |-------------------------------------- | | 1 | VS+ | Remote Sense (+) 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
D38 and D39 for DB9 Loopback
Sense divider is 0.595*Vin 5V * 0.595 = 2.976V
Connector_JST:JST_XH_B2B-XH-AM_1x02_P2.50mm_Vertical
SSR1_PWM
Reworked into V1.2
V_ASSY_VERSIONING Control 1.2 voltage = 1.055V
Heart beat, Loop OK
Breadboarding Area Patterned off of solderless breadboard
To chassis mounted +24V.
RESET D46 DC D47 CS D48
One Wire Thermocouple amplifiter DATA is bidirectional GPIO
MAX31855
Remote Sense 2
Due pin 22
MAX31850
