PubInv/high-amp-controller-board/Fan controller.kicad_sch

## KiCad design Fan controller.kicad_sch (2025-05-26)

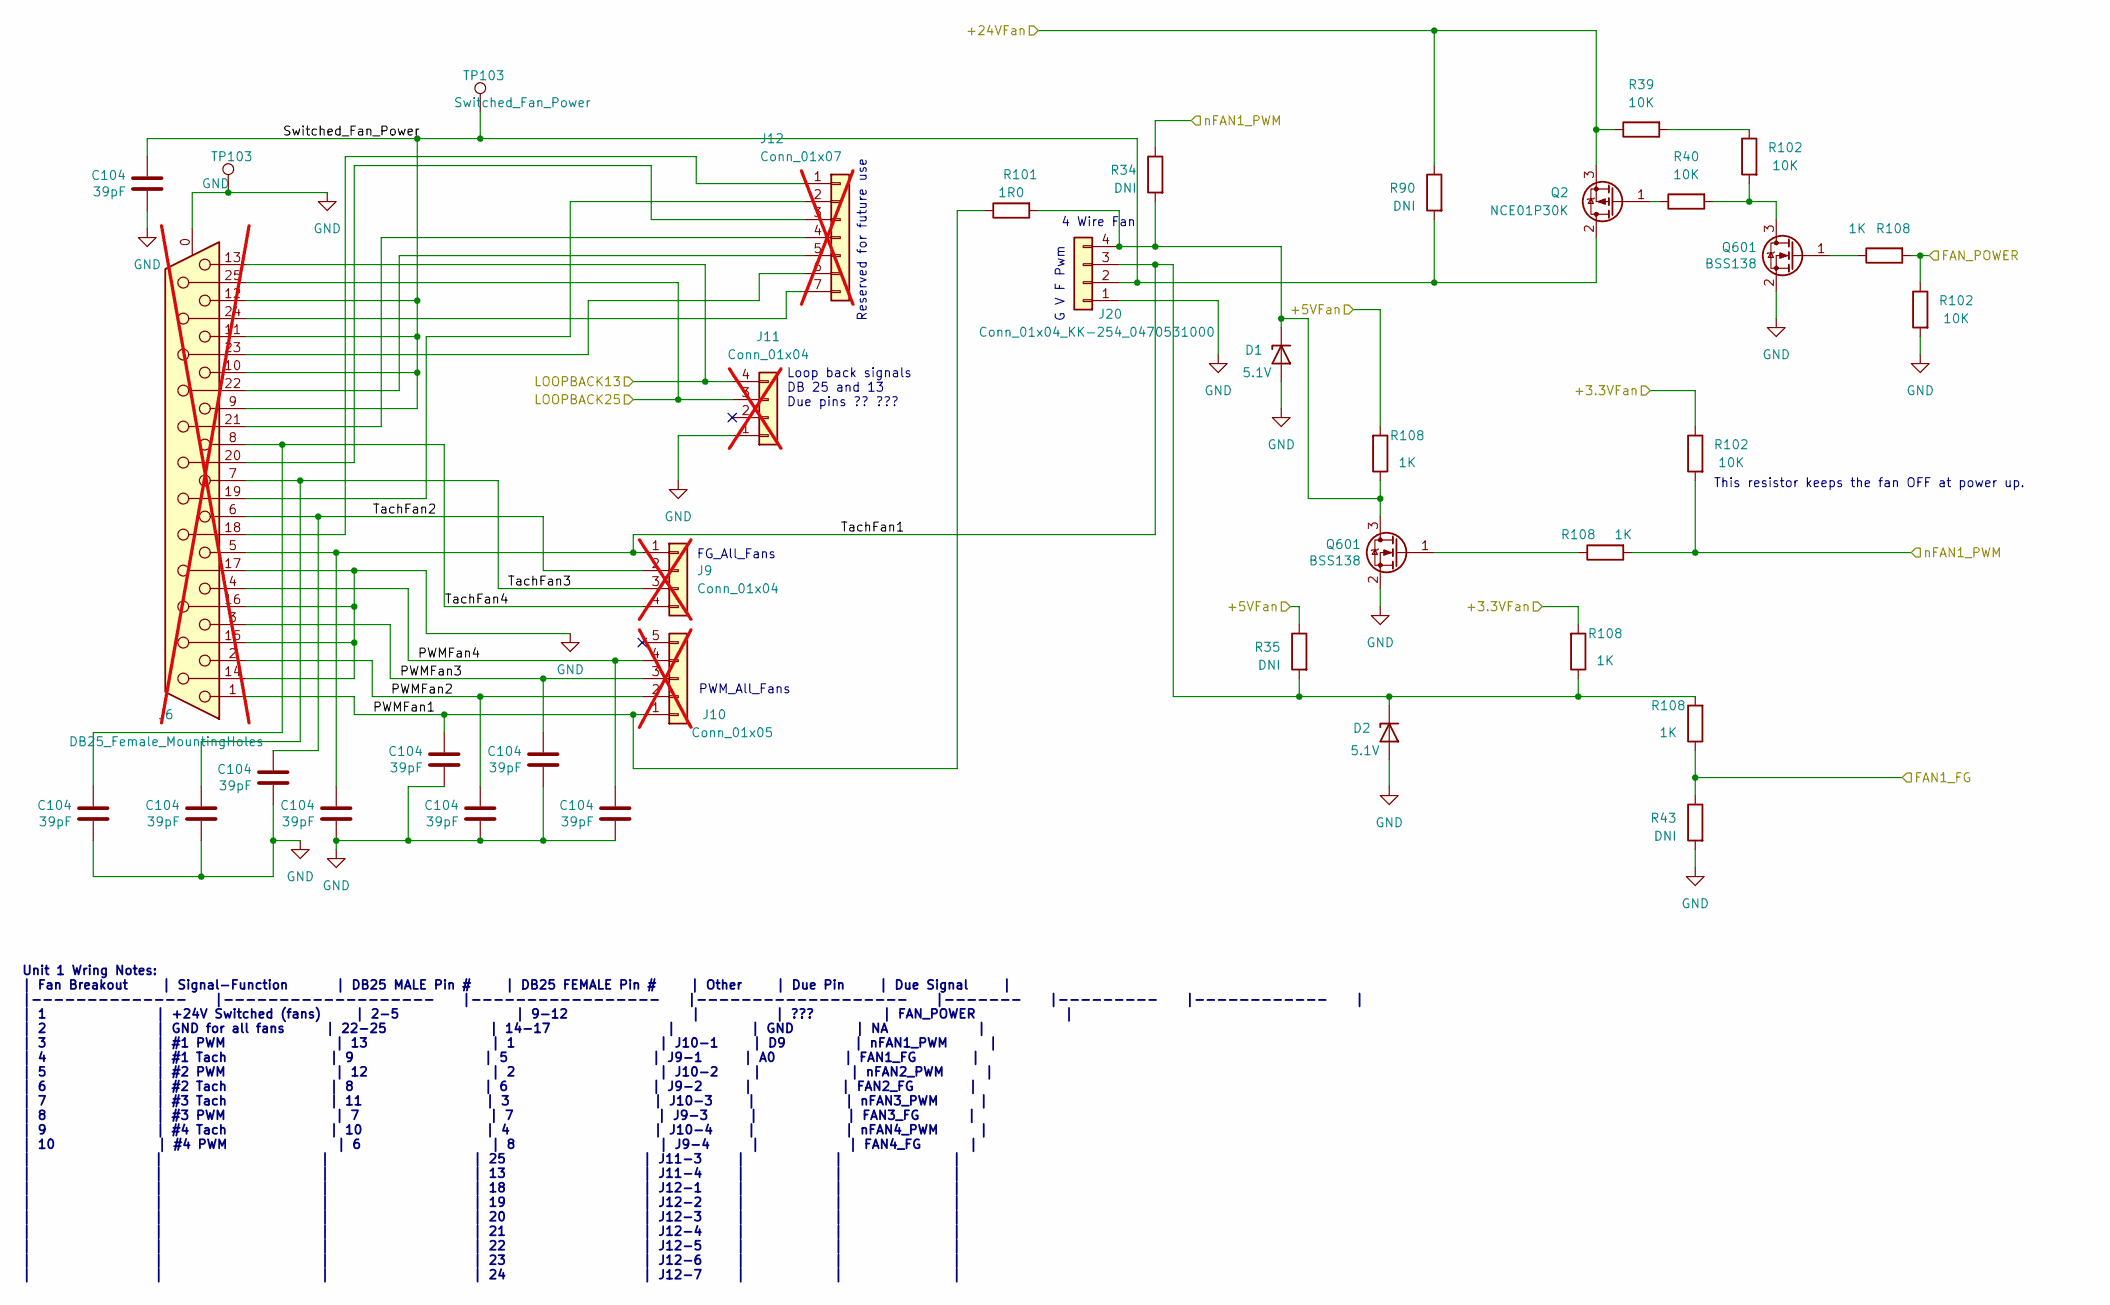
[picture p36: schematic Fan controller.kicad_sch]

Parts:
C104: 39pF; C_0603_1608Metric_Pad1.08x0.95mm_HandSolder; MPN CC0603JRNPO9BN390
D1, D2: 5.1V; D_MiniMELF; MPN ZMM5231
J6: DB25_Female_MountingHoles; DSUB-25_Female_Horizontal_P2.77x2.84mm_EdgePinOffset4.94mm_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; MPN D-DMR025PF-D002; not fitted
J9, J11: Conn_01x04; PinHeader_1x04_P2.54mm_Vertical; MPN HB-PH3-25414PB2GOP; not fitted
J10: Conn_01x05; PinHeader_1x05_P2.54mm_Vertical; MPN PM254-1-05-Z-8.5; not fitted
J12: Conn_01x07; PinHeader_1x07_P2.54mm_Vertical; not fitted
J20: Conn_01x04_KK-254_0470531000; Molex_KK-254_0470531000_1x04_P2.54mm_Vertical_ForFAN; MPN 0470531000
Q2: NCE01P30K; TO-252-2; MPN NCE01P30K
Q601: BSS138; SOT-23; MPN BSS138
R34, R35, R43, R90: DNI; R_0603_1608Metric_Pad0.98x0.95mm_HandSolder
R39, R40, R102: 10K; R_0603_1608Metric_Pad0.98x0.95mm_HandSolder; MPN RMC060310KFN
R101: 1R0; R_0603_1608Metric_Pad0.98x0.95mm_HandSolder; MPN RMC060315%N
R108: 1K; R_0603_1608Metric_Pad0.98x0.95mm_HandSolder; MPN RMC06031K1%N
TP103: Switched_Fan_Power; TestPoint_Loop_D2.54mm_Drill1.5mm_Beaded; MPN RH-5000

Connections:
+3.3VFan: R102.1, R108.2
+5VFan: R35.1, R108.2
+24VFan: Q2.3 (S), R39.1, R90.1
FAN1_FG: R43.1, R108.1
FAN_POWER: R102.1, R108.2
GND: C104.2, D1.2 (A), D2.2 (A), J6.0 (PAD), J6.14, J6.15, J6.16, J6.17, J11.1, J20.1, Q601.2 (S), R43.2, R102.2, TP103.1
LOOPBACK13: J6.13, J11.4
LOOPBACK25: J6.25, J11.3
unnamed: D1.1 (K), J20.4, Q601.3 (D), R34.2, R101.2, R108.1
unnamed: J6.18, J12.1
unnamed: J6.19, J12.2
unnamed: J6.20, J12.3
unnamed: J6.21, J12.4
unnamed: J6.22, J12.5
unnamed: J6.23, J12.6
unnamed: J6.24, J12.7
unnamed: Q2.1 (G), R40.1
unnamed: Q601.1 (G), R108.1
unnamed: Q601.3 (D), R40.2, R102.2
unnamed: R39.2, R102.1
PWMFan1: C104.1, J6.1, J10.1, R101.1
PWMFan2: C104.1, J6.2, J10.2
PWMFan3: C104.1, J6.3, J10.3
PWMFan4: C104.1, J6.4, J10.4
Switched_Fan_Power: C104.1, J6.9, J6.10, J6.11, J6.12, J20.2, Q2.2 (D), R90.2, TP103.1
TachFan1: C104.1, D2.1 (K), J6.5, J9.1, J20.3, R35.2, R108.1, R108.2
TachFan2: C104.1, J6.6, J9.2
TachFan3: C104.1, J6.7, J9.3
TachFan4: C104.1, J6.8, J9.4
nFAN1_PWM: R34.1, R102.2, R108.2

Notes on the sheet:
FG_All_Fans
Loop back signals DB 25 and 13 Due pins ?? ???
4 Wire Fan
PWM_All_Fans
Reserved for future use
G V F Pwm
Unit 1 Wring Notes: | Fan Breakout | Signal-Function | DB25 MALE Pin # | DB25 FEMALE Pin # | Other | Due Pin | Due Signal | |-------------- |------------------- |----------------- |------------------- |------- |--------- |------------ | | 1 | +24V Switched (fans) | 2-5 | 9-12 | | ??? | FAN_POWER | 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
This resistor keeps the fan OFF at power up.
