PubInv/high-amp-controller-board/I2C_Level_Shifter.kicad_sch

## KiCad design I2C_Level_Shifter.kicad_sch (2025-05-26)

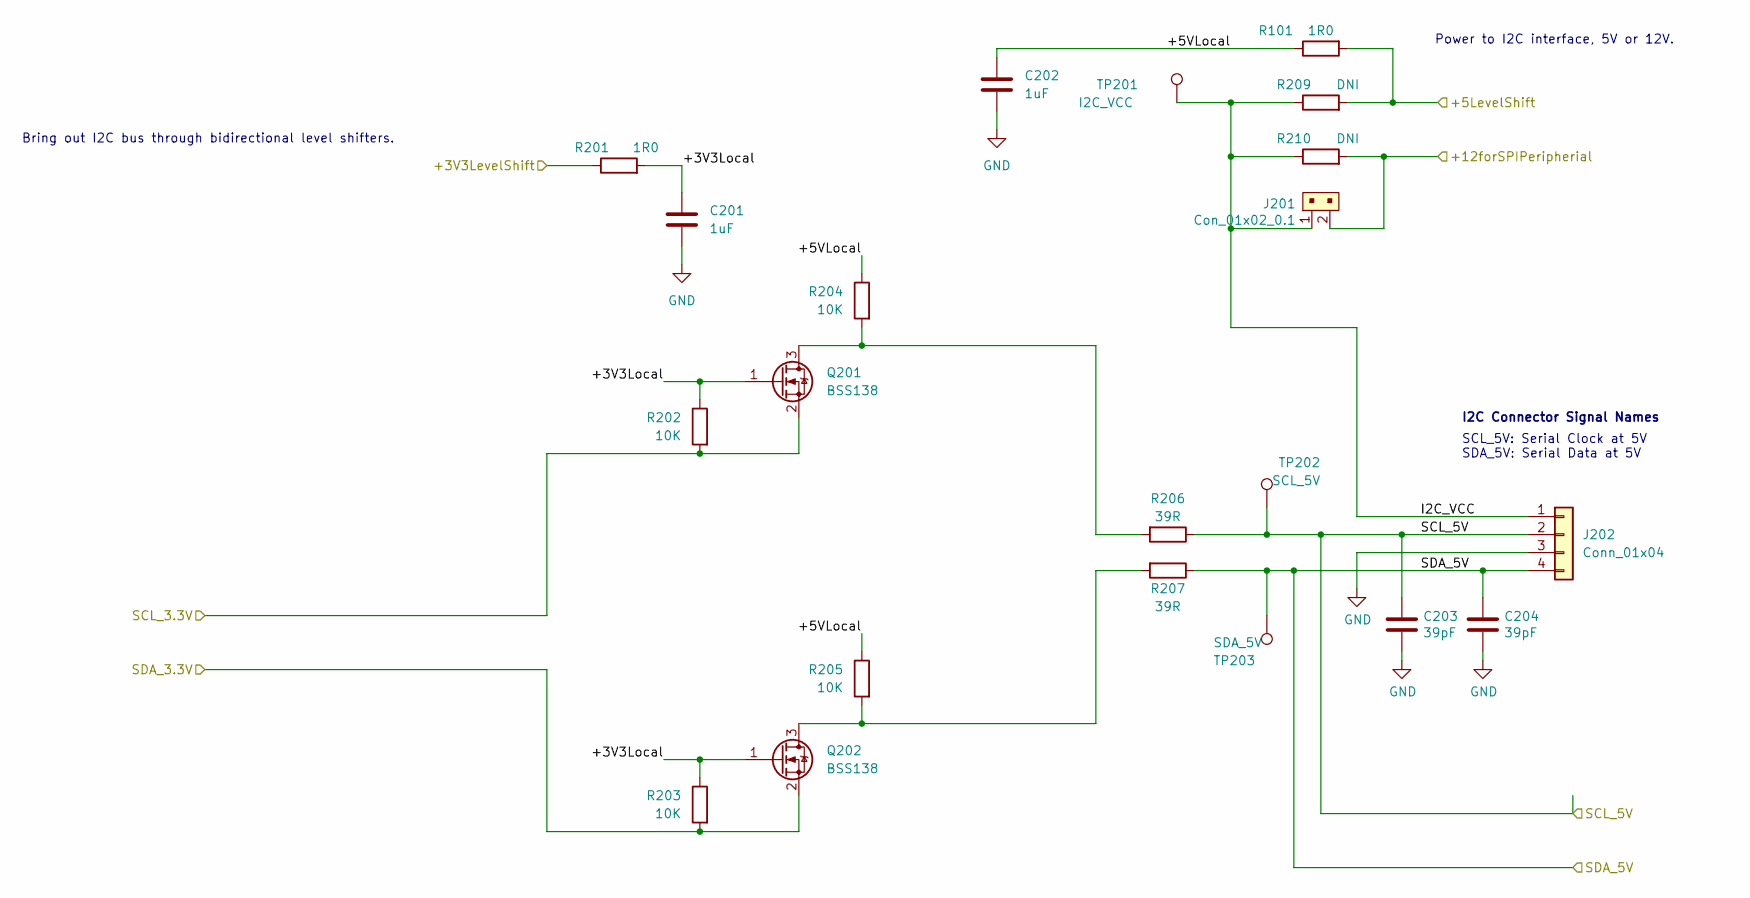
[picture p37: schematic I2C_Level_Shifter.kicad_sch]

Parts:
C201, C202: 1uF; C_0603_1608Metric_Pad1.08x0.95mm_HandSolder; MPN CC0603JRX7R9BB104
C203, C204: 39pF; C_0603_1608Metric_Pad1.08x0.95mm_HandSolder; MPN CC0603JRNPO9BN390
J201: Con_01x02_0.1; PinHeader_1x02_P2.54mm_Vertical; MPN PZ254V-11-02P
J202: Conn_01x04; PinHeader_1x04_P2.54mm_Vertical; MPN HB-PH3-25414PB2GOP
Q201, Q202: BSS138; SOT-23; MPN BSS138
R101, R201: 1R0; R_0603_1608Metric_Pad0.98x0.95mm_HandSolder; MPN RMC060315%N
R202, R203, R204, R205: 10K; R_0603_1608Metric_Pad0.98x0.95mm_HandSolder; MPN RMC060310KFN
R206, R207: 39R; R_0603_1608Metric_Pad0.98x0.95mm_HandSolder; MPN RMC0603391%N
R209, R210: DNI; R_0603_1608Metric_Pad0.98x0.95mm_HandSolder
TP201: I2C_VCC; TestPoint_Loop_D2.54mm_Drill1.5mm_Beaded; MPN RH-5000
TP202: SCL_5V; TestPoint_Loop_D2.54mm_Drill1.5mm_Beaded; MPN RH-5000
TP203: SDA_5V; TestPoint_Loop_D2.54mm_Drill1.5mm_Beaded; MPN RH-5000

Connections:
+3V3LevelShift: R201.1
+3V3Local: C201.1, Q201.1 (G), Q202.1 (G), R201.2, R202.1, R203.1
+5LevelShift: R101.2, R209.2
+5VLocal: C202.1, R101.1, R204.1, R205.1
+12forSPIPeripherial: J201.2, R210.2
GND: C201.2, C202.2, C203.2, C204.2, J202.3
I2C_VCC: J201.1, J202.1, R209.1, R210.1, TP201.1
unnamed: Q201.3 (D), R204.2, R206.2
unnamed: Q202.3 (D), R205.2, R207.2
SCL_3.3V: Q201.2 (S), R202.2
SCL_5V: C203.1, J202.2, R206.1, TP202.1
SDA_3.3V: Q202.2 (S), R203.2
SDA_5V: C204.1, J202.4, R207.1, TP203.1

Notes on the sheet:
Bring out I2C bus through bidirectional level shifters.
I2C Connector Signal Names
Power to I2C interface, 5V or 12V.
SCL_5V: Serial Clock at 5V SDA_5V: Serial Data at 5V
