PubInv/high-amp-controller-board/SPI_ControllerLevel_Shifter.kicad_sch

## KiCad design SPI_ControllerLevel_Shifter.kicad_sch (2025-05-26)

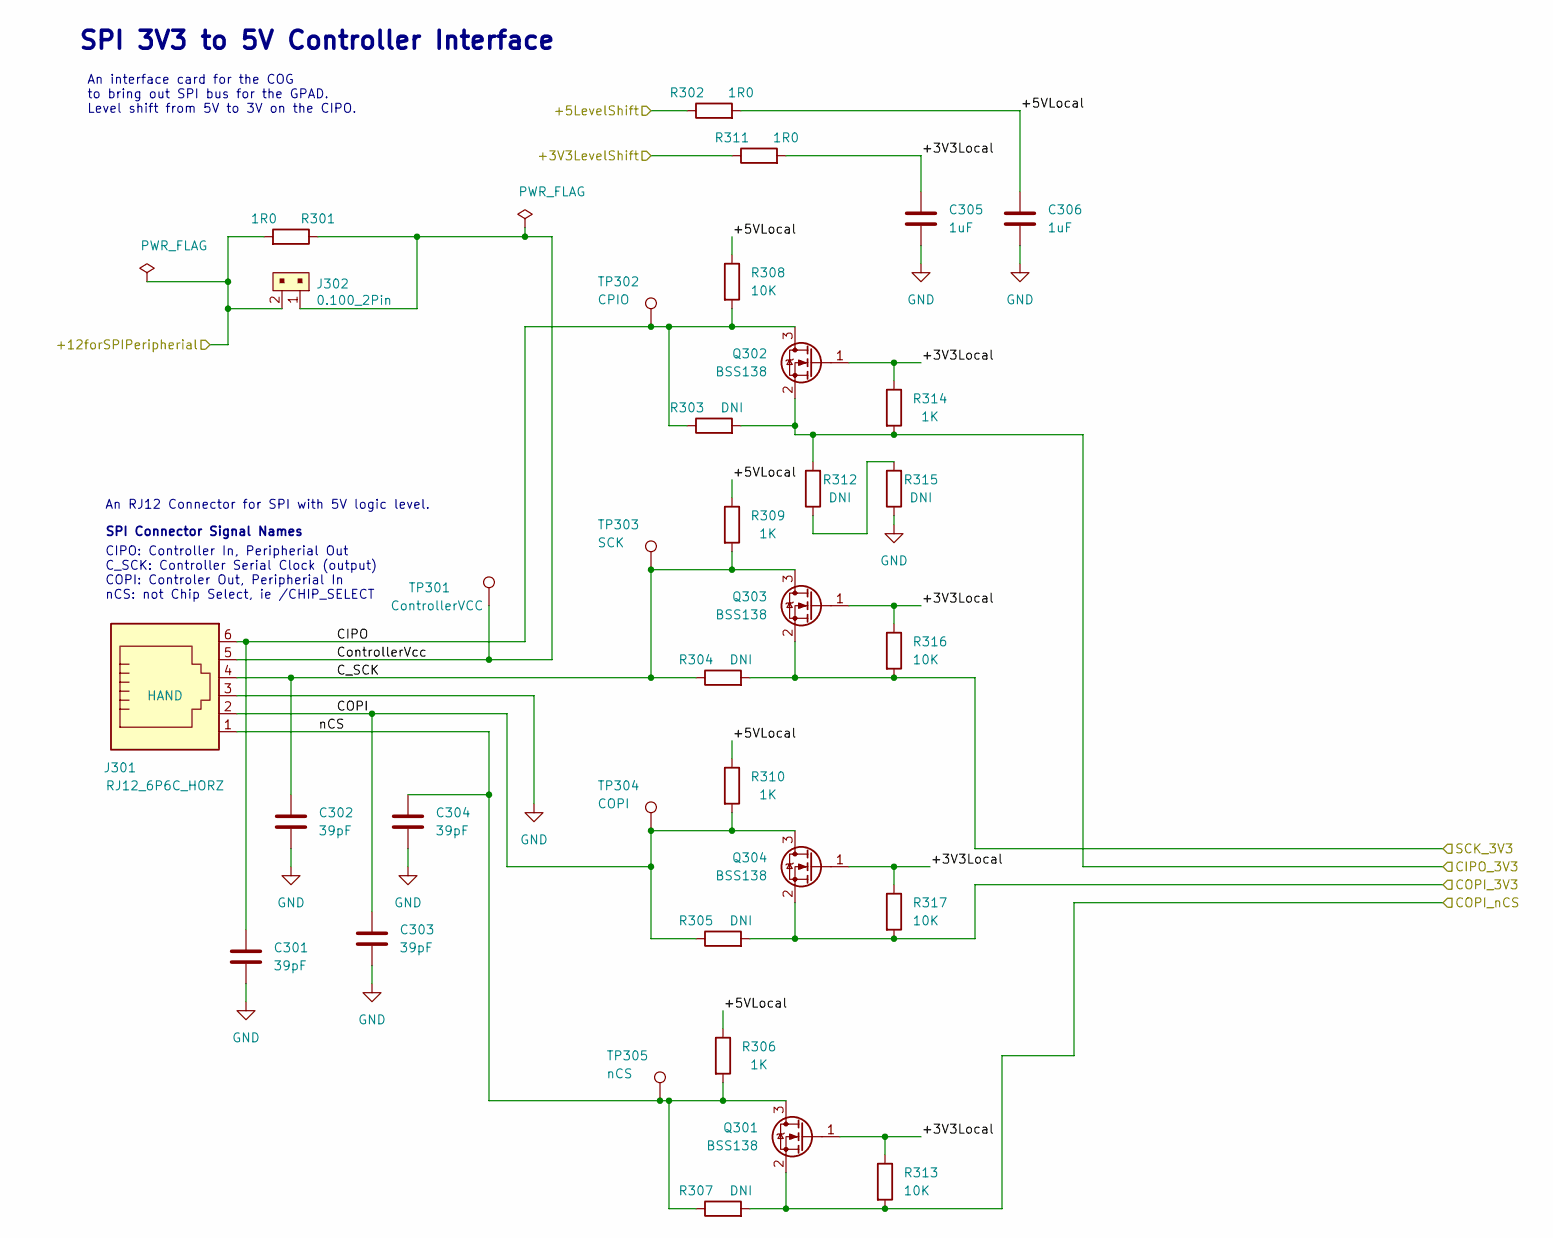
[picture p38: schematic SPI_ControllerLevel_Shifter.kicad_sch]

Parts:
C301, C302, C303, C304: 39pF; C_0603_1608Metric_Pad1.08x0.95mm_HandSolder; MPN CC0603JRNPO9BN390
C305, C306: 1uF; C_0603_1608Metric_Pad1.08x0.95mm_HandSolder; MPN CC0603JRX7R9BB104
J301: RJ12_6P6C_HORZ; RJ12_Amphenol_54601; MPN 5555165-1
J302: 0.100_2Pin; PinHeader_1x02_P2.54mm_Vertical; MPN 68000-102HLF
Q301, Q302, Q303, Q304: BSS138; SOT-23; MPN BSS138
R301, R302, R311: 1R0; R_0603_1608Metric_Pad0.98x0.95mm_HandSolder; MPN RMC060315%N
R303, R304, R305, R307, R312, R315: DNI; R_0603_1608Metric_Pad0.98x0.95mm_HandSolder; MPN RMC06031K1%N
R306, R309, R310, R314: 1K; R_0603_1608Metric_Pad0.98x0.95mm_HandSolder; MPN RMC06031K1%N
R308, R313, R316, R317: 10K; R_0603_1608Metric_Pad0.98x0.95mm_HandSolder; MPN RMC060310KFN
TP301: ControllerVCC; TestPoint_Loop_D2.54mm_Drill1.5mm_Beaded
TP302: CPIO; TestPoint_Loop_D2.54mm_Drill1.5mm_Beaded
TP303: SCK; TestPoint_Loop_D2.54mm_Drill1.5mm_Beaded
TP304: COPI; TestPoint_Loop_D2.54mm_Drill1.5mm_Beaded
TP305: nCS; TestPoint_Loop_D2.54mm_Drill1.5mm_Beaded

Connections:
+3V3LevelShift: R311.1
+3V3Local: C305.1, Q301.1 (G), Q302.1 (G), Q303.1 (G), Q304.1 (G), R311.2, R313.1, R314.1, R316.1, R317.1
+5LevelShift: R302.1
+5VLocal: C306.1, R302.2, R306.1, R308.1, R309.1, R310.1
+12forSPIPeripherial: J302.2, R301.2
CIPO: C301.1, J301.6, Q302.3 (D), R303.1, R308.2, TP302.1
CIPO_3V3: Q302.2 (S), R303.2, R312.2, R314.2
COPI: C303.1, J301.2, Q304.3 (D), R305.1, R310.2, TP304.1
COPI_3V3: Q304.2 (S), R305.2, R317.2
COPI_nCS: Q301.2 (S), R307.2, R313.2
C_SCK: C302.1, J301.4, Q303.3 (D), R304.1, R309.2, TP303.1
ControllerVcc: J301.5, J302.1, R301.1, TP301.1
GND: C301.2, C302.2, C303.2, C304.2, C305.2, C306.2, J301.3, R315.1
unnamed: R312.1, R315.2
SCK_3V3: Q303.2 (S), R304.2, R316.2
nCS: C304.1, J301.1, Q301.3 (D), R306.2, R307.1, TP305.1

Notes on the sheet:
CIPO: Controller In, Peripherial Out C_SCK: Controller Serial Clock (output) COPI: Controler Out, Peripherial In nCS: not Chip Select, ie /CHIP_SELECT
An RJ12 Connector for SPI with 5V logic level.
SPI Connector Signal Names
SPI 3V3 to 5V Controller Interface
An interface card for the COG to bring out SPI bus for the GPAD. Level shift from 5V to 3V on the CIPO.
