PubInv/high-amp-controller-board/SSR Interface.kicad_sch

## KiCad design SSR Interface.kicad_sch (2025-05-26)

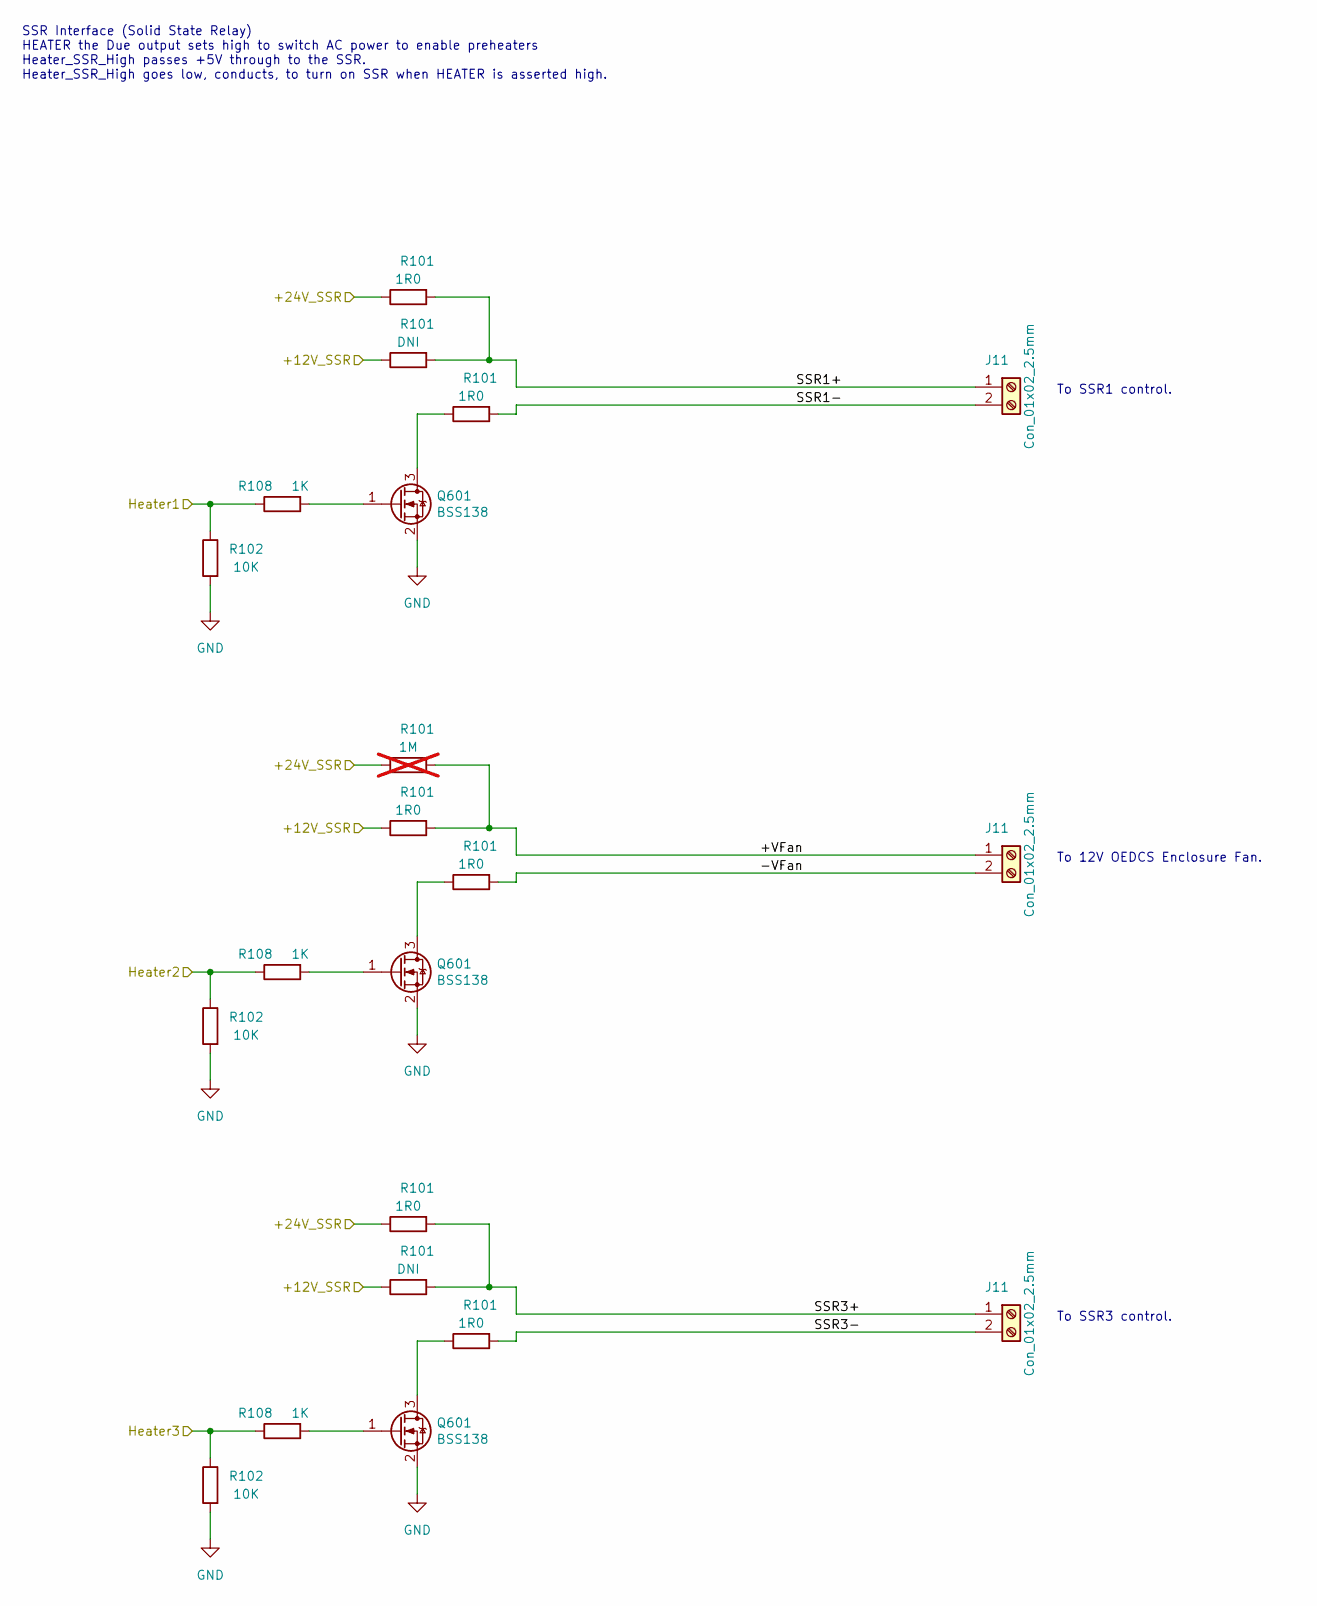
[picture p39: schematic SSR Interface.kicad_sch]

Parts:
J11: Con_01x02_2.5mm; JST_XH_B2B-XH-AM_1x02_P2.50mm_Vertical; MPN B2B-XH-A-GU
Q601: BSS138; SOT-23; MPN BSS138
R101: DNI; R_0603_1608Metric_Pad0.98x0.95mm_HandSolder; MPN RMC060315%N
R102: 10K; R_0603_1608Metric_Pad0.98x0.95mm_HandSolder; MPN RMC060310KFN
R108: 1K; R_0603_1608Metric_Pad0.98x0.95mm_HandSolder; MPN RMC06031K1%N

Connections:
+12V_SSR: R101.1
+24V_SSR: R101.1
+VFan: J11.1, R101.2
-VFan: J11.2, R101.2
GND: Q601.2 (S), R102.2
Heater1: R102.1, R108.1
Heater2: R102.1, R108.1
Heater3: R102.1, R108.1
unnamed: Q601.1 (G), R108.2
unnamed: Q601.3 (D), R101.1
SSR1+: J11.1, R101.2
SSR1-: J11.2, R101.2
SSR3+: J11.1, R101.2
SSR3-: J11.2, R101.2

Notes on the sheet:
To 12V OEDCS Enclosure Fan.
SSR Interface (Solid State Relay) HEATER the Due output sets high to switch AC power to enable preheaters Heater_SSR_High passes +5V through to the SSR. Heater_SSR_High goes low, conducts, to turn on SSR when HEATER is asserted high.
To SSR1 control.
To SSR3 control.
