PubInv/high-amp-controller-board/display_interface.kicad_sch

## KiCad design display_interface.kicad_sch (2025-05-26)

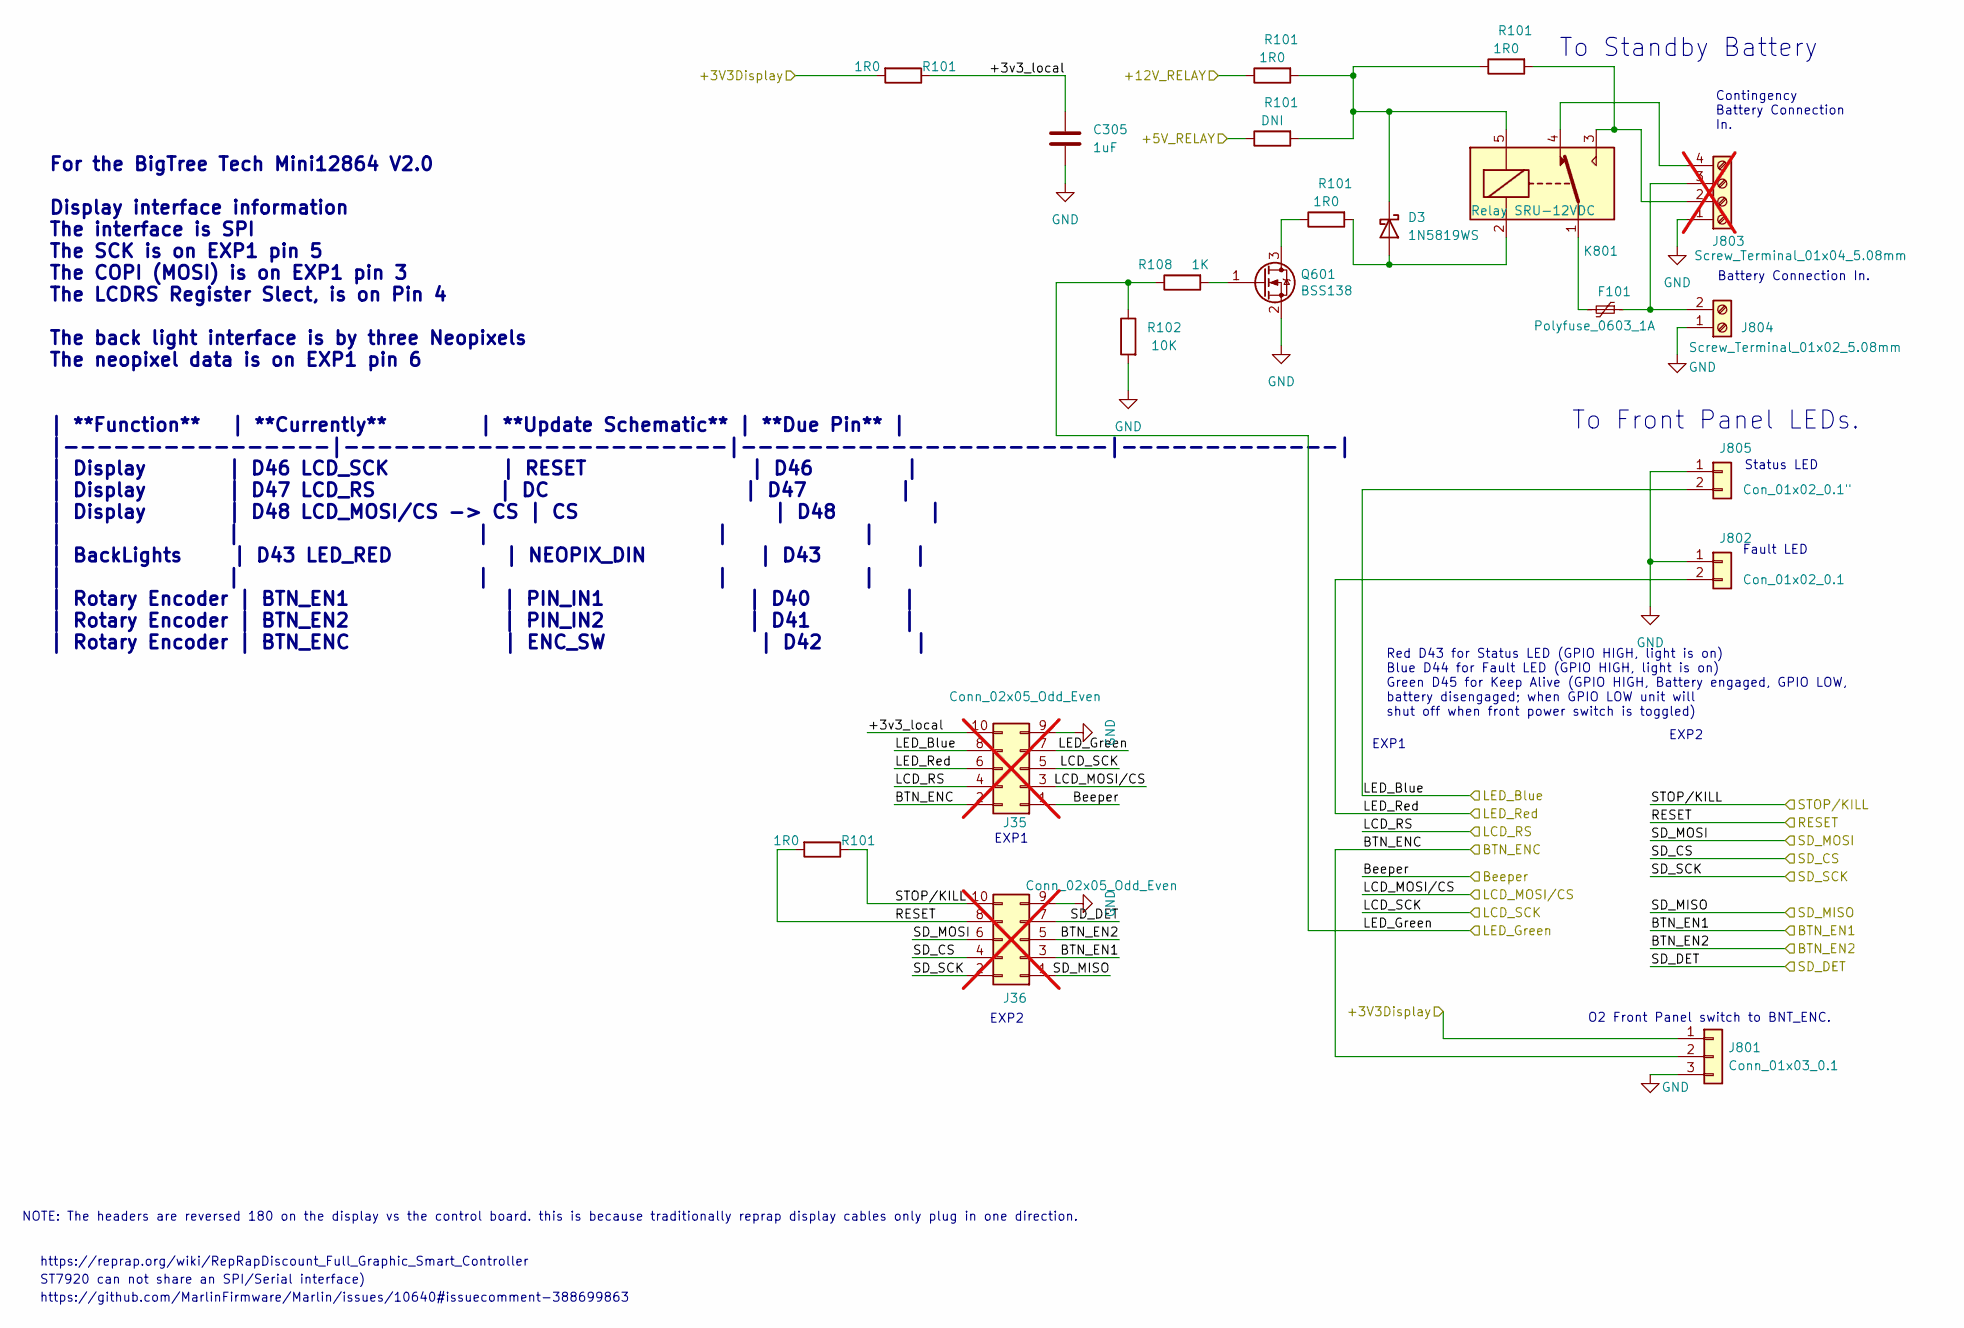
[picture p40: schematic display_interface.kicad_sch]

Parts:
C305: 1uF; C_0603_1608Metric_Pad1.08x0.95mm_HandSolder; MPN CC0603JRX7R9BB104
D3: 1N5819WS; D_SOD-323; MPN 1N5819WS
F101: Polyfuse_0603_1A; Fuse_0603_1608Metric; MPN 0603L100SLYR
J35, J36: Conn_02x05_Odd_Even; IDC-Header_2x05_P2.54mm_Vertical; MPN 61201021621; not fitted
J801: Conn_01x03_0.1; PinHeader_1x03_P2.54mm_Vertical; MPN HB-PH3-25413PB2GOP
J802: Con_01x02_0.1; PinHeader_1x02_P2.54mm_Vertical; MPN PZ254V-11-02P
J803: Screw_Terminal_01x04_5.08mm; TerminalBlock_Phoenix_MKDS-1,5-4-5.08_1x04_P5.08mm_Horizont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; MPN 1715747; not fitted
J804: Screw_Terminal_01x02_5.08mm; TerminalBlock_Phoenix_MKDS-1,5-2-5.08_1x02_P5.08mm_Horizont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; MPN JL500-50802G01
J805: Con_01x02_0.1"; PinHeader_1x02_P2.54mm_Vertical; MPN PZ254V-11-02P
K801: Relay SRU-12VDC; Relay_SPDT_Omron-G5LE-1; MPN SRU-12VDC-SL-C
Q601: BSS138; SOT-23; MPN BSS138
R101: 1R0; R_0603_1608Metric_Pad0.98x0.95mm_HandSolder; MPN RMC060315%N
R102: 10K; R_0603_1608Metric_Pad0.98x0.95mm_HandSolder; MPN RMC060310KFN
R108: 1K; R_0603_1608Metric_Pad0.98x0.95mm_HandSolder; MPN RMC06031K1%N

Connections:
+3V3Display: J801.1, R101.2
+3v3_local: C305.1, J35.10, R101.1
+5V_RELAY: R101.1
+12V_RELAY: R101.1
BTN_EN1: J36.3
BTN_EN2: J36.5
BTN_ENC: J35.2, J801.2
Beeper: J35.1
GND: C305.2, J35.9, J36.9, J801.3, J802.1, J803.1, J804.1, J805.1, Q601.2 (S), R102.2
LCD_MOSI/CS: J35.3
LCD_RS: J35.4
LCD_SCK: J35.5
LED_Blue: J35.8, J805.2
LED_Green: J35.7, R102.1, R108.1
LED_Red: J35.6, J802.2
unnamed: D3.1 (K), K801.5, R101.1, R101.2
unnamed: D3.2 (A), K801.2, R101.2
unnamed: F101.1, J803.3, J804.2
unnamed: F101.2, K801.1
unnamed: J803.2, K801.3, R101.2
unnamed: J803.4, K801.4
unnamed: Q601.1 (G), R108.2
unnamed: Q601.3 (D), R101.1
RESET: J36.8, R101.2
SD_CS: J36.4
SD_DET: J36.7
SD_MISO: J36.1
SD_MOSI: J36.6
SD_SCK: J36.2
STOP/KILL: J36.10, R101.1

Notes on the sheet:
Red D43 for Status LED (GPIO HIGH, light is on) Blue D44 for Fault LED (GPIO HIGH, light is on) Green D45 for Keep Alive (GPIO HIGH, Battery engaged, GPIO LOW, battery disengaged; when GPIO LOW unit will shut off when front power switch is toggled)
Fault LED
O2 Front Panel switch to BNT_ENC.
Contingency Battery Connection In.
EXP2
https://reprap.org/wiki/RepRapDiscount_Full_Graphic_Smart_Controller
To Front Panel LEDs.
For the BigTree Tech Mini12864 V2.0 Display interface information The interface is SPI The SCK is on EXP1 pin 5 The COPI (MOSI) is on EXP1 pin 3 The LCDRS Register Slect, is on Pin 4 The back light interface is by three Neopixels The neopixel data is on EXP1 pin 6 | **Function** | **Currently** | *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
Battery Connection In.
EXP1
ST7920 can not share an SPI/Serial interface)
Status LED
To Standby Battery
https://github.com/MarlinFirmware/Marlin/issues/10640#issuecomment-388699863
NOTE: The headers are reversed 180 on the display vs the control board. this is because traditionally reprap display cables only plug in one direction.
