PubInv/high-amp-controller-board/Manufacturing_Files/FabricationPhotos/20250130_080216.jpg

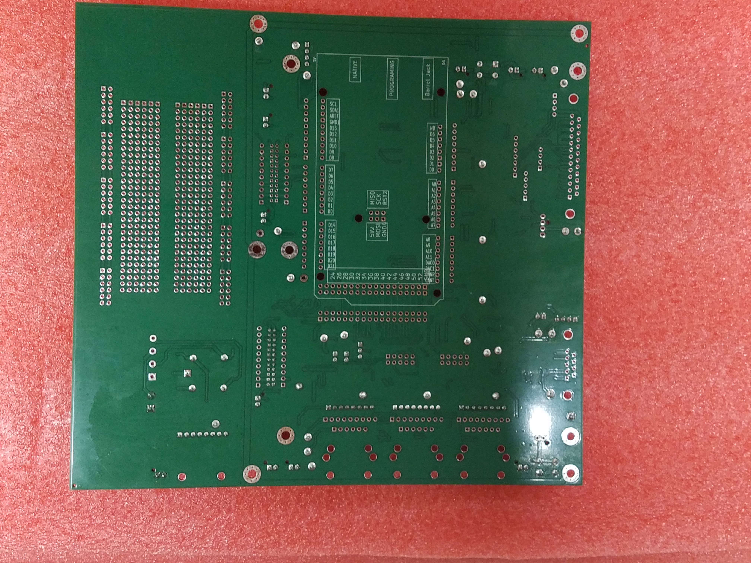
Manufacturing_Files/FabricationPhotos/20250130_080216.jpg
